nickdnj/3280-kiosk/mechanical/rev1-design-study.html

ConceptConcurrent 3280 Exhibit KioskRev 12026-08-28

# The kiosk is its own product

A self-contained enclosure — display, Pi, power, three buttons — built and bench-tested on a table, then hung on the front of the 3280's closed factory door. The machine is not opened, not drilled, not modified. The buttons are the datum: ADA reach sets their height, and the height sets where everything else goes.

Display size

22″ 24″ 27″ 32″

Button height

38″ AFF

## 01Front elevation

The kiosk on the closed factory door, drawn to scale against the 71″ cabinet with a 5′8″ figure for reference. Switch sizes above — this is the view that decides the question.

Sheet R1-01 · front elevation · cabinet 24 × 71 OEM, door 24.3 wide derived · buttons are the placement datum

The 3280 stays visually dominant. That is the whole design constraint of this view: a visitor should read a historic minicomputer with an interpretation device added to it, not a monitor wearing a cabinet.

The button line is the datum. The kiosk is placed from the bottom up: the buttons go where a hand can reach them, and the screen goes wherever that leaves it. Section 02 sets that height from the ADA reach range; the shaded band on the drawing is the legal 15″–48″ window.

Push the button slider up and the 32″ runs out of door before the others do — that constraint, not screen area, is what separates the sizes.

## 02Button height drives placement

The buttons are the datum. Where a visitor's hand goes decides where the kiosk sits, and everything above it follows. Move the slider — the elevation, the fit check and the table all follow the button line.

### The rule

ADA 2010 §308 puts operable parts between 15″ and 48″ above the finished floor. Unobstructed forward reach and unobstructed side reach give the same 48″ maximum, so the approach doesn't change the number. The 3280's face is flat and floor-standing with no knee clearance underneath, so a visitor in a wheelchair makes a parallel approach and reaches sideways — still 48″.

48″ is a ceiling, not a target

Designing at the maximum satisfies the letter of the standard and serves tall standing adults. It fails seated visitors and children, who are exactly the people the reach range exists for.

Provision | Requirement | Where it lands on this design
§308.2.1 / §308.3.1 unobstructed reach | 15″ min · 48″ max AFF | Sets the legal window for the button centreline. Binding at the top for the 32″.
§309.4 operable parts | one hand · no tight grasping, pinching or twisting · ≤ 5 lbf | A 30 mm anti-vandal momentary switch is typically well under 1 lbf. Check the actuation force on the spec sheet — some heavy industrial switches are stiff.
§305 clear floor space | 30″ × 48″ at the control | A museum floor requirement, not an enclosure one. Confirm the approach to the cabinet is kept clear when the exhibit is sited.
§307.2 protruding objects | leading edge above 27″ → 4″ max projection | Constrains the mount. See below.

### Rev 1 target — 38″ AFF

- 10″ below the ADA maximum. That margin absorbs mount tolerance, floor variation and the fact that nobody has built this yet.
- At or just above elbow height for a shorter standing adult, and a natural reach-down for a taller one.
- Comfortably inside a seated visitor's reach, and reachable by a child of about eight.

It improves the screen too

Buttons at 38″ put the 24″ screen centre at 51.5″. Adult seated eye height is roughly 47–51″, so the screen is very nearly centred on a seated visitor, while a standing adult looks down about 11° — normal reading posture. The ADA-driven placement is better for everyone than the 40″ this study first drew.

### What it costs the mount

With the buttons at 38″ the kiosk's bottom edge sits at 34.75″ AFF — above the 27″ threshold, so §307.2 caps the projection into a circulation path at 4″. With the recommended 3 mm ACM face (§06) the enclosure is 3.25″ deep, leaving 0.75″ for the mounting adapter — and a plywood face instead would cut that to 0.5″.

Worth asking, not worth assuming

§307.2 exists to stop someone with a cane walking into an object their sweep misses. The 3280 is floor-standing and cane-detectable, and a visitor is stopped by the cabinet before the kiosk is in reach — so the hazard the rule targets may not apply here. That is the museum's accessibility coordinator's call, not ours. Design the adapter to 4″ total, and ask.

### Placement math

The button centreline sits 3.25″ above the bottom of the enclosure, and the door face runs from about 3″ to 71.15″ AFF. So for a button height B and a kiosk height KH:

kiosk bottom = B − 3.25″
kiosk top = B + KH − 3.25″ ≤ 71.15″
→ B ≤ 74.40″ − KH

### The window each display size leaves you

| 22″ | 24″ | 27″ | 32″
Kiosk height | 26.69″ | 28.69″ | 31.48″ | 35.40″
Highest button the geometry allows | 47.7″ | 45.7″ | 42.9″ | 39.0″
Legal button window | 15 – 47.7″ | 15 – 45.7″ | 15 – 42.9″ | 15 – 39.0″
Of the 34–44″ comfort band | all of it | all of it | 34 – 42.9″ | 34 – 39.0″
Headroom below the door top

Correction to the earlier study

With the buttons at a properly-chosen 38″ rather than the 40″ first drawn, the 32″ fits — its top lands at 70.15″, an inch under the door. It is not a geometric failure and this study should not have called it one.

What the 32″ actually costs is freedom. It clips half the comfort band away, and the remaining inch of headroom is inside normal build tolerance. The case against it now rests on weight and proportion alone — §08.

## 03Kiosk, standalone

The enclosure by itself. Everything in this drawing is buildable and testable before the 3280 is involved at all.

Sheet R1-02 · kiosk front elevation

Sheet R1-03 · button row detail · cut into the face plate

### Why the buttons are cut straight into the face plate

An earlier version of this design put them on a separate plate behind an aperture, to insure against getting the switch cutout wrong. That was over-engineered. It bought one thing and charged three for it.

Stiffness was the real cost. Cutting both a 12.17 × 21.24 window and an 11.87 × 3.00 aperture out of one 3 mm sheet left a 1.35″ web as the only material joining the side rails below the screen. One piece leaves 2.25″ above the buttons and 2.65″ below. It also meant a second part on the invoice, six more holes, a second set of cleats, and a plate to align square in an aperture.

And the wear argument didn't hold. Anti-vandal switches are rated for millions of cycles, and when one fails you replace the switch, through the same hole. The plate only needs replacing if the hole itself is damaged, which essentially doesn't happen.

The insurance is better bought by confirming the cutout before ordering than by designing around not knowing it.

30 mm anti-vandal stainless, momentary, 30.5 mm hole. A big public target, industrial life, about $10 each, and a hole size so standard that any replacement in 2033 will fit. Labels engraved into the plate — stickers peel.

Flat, not angled. An angled lower surface adds a bevelled joint, adds depth at the bottom, and complicates the mount's load path. At 38″ AFF a flat face is comfortable for a standing adult. Revisit only if observation says otherwise.

No fasteners on the visitor-facing surface. The face plate is captured from behind — nothing on the front is a screw a bored twelve-year-old can turn.

A cleat row sits between the window and the buttons. Three fixings onto a plywood rail, so the panel takes the press load instead of flexing every time somebody pushes a button. It clears the switch bodies, which stand about an inch proud behind the plate.

## 04Side section

Depth decides how far the kiosk stands off the machine — every eighth of an inch here is visible, and ADA §307.2 caps the whole projection at 4″. Drawn with the recommended 3 mm ACM face (§06); a plywood face costs another 3/8″.

Sheet R1-04 · side section · depth to 3.5″ target · mounting interface left blank by intent

### What forces the depth

- The monitor's thickest point — 1.6″ to 2.3″. The only hard number in the stack, and the reason depth grows with screen size even though the panel doesn't.
- Cable bend at the connectors — 0.75″ to 1.75″. The one you can design away, and the difference between 3.5″ and 4.5″. Route HDMI and DC downward into the button bay with right-angle plugs.
- Face plate + rear panel. A 3 mm ACM face and a 1/2″ ply rear come to 0.62″ together. A plywood face instead makes it 1.0″ — and that 3/8″ comes straight out of the mounting adapter's budget.

### What does not

- The Raspberry Pi. 0.65″ tall, and it does not go behind the monitor. It goes in the button bay on a slide-out tray, where 4″ of depth is otherwise doing nothing. Design the enclosure around fitting a Pi behind the panel and you will build it an inch too deep.

Reversed from earlier work

The monitor stays cased. De-casing buys about 1.2″ and costs the EMI shielding, the thermal design, the power board's own enclosure, and any hope of a volunteer replacing it. Not worth it.

Depth target | Verdict
2.50″ | No. Requires a sub-1.4″ monitor, a 1/8″ face and zero service gap.
3.00″ | Achievable at 22–24″ with a slim monitor, right-angle cables and down-routing. No margin.
3.25″ | The design target, with a 3 mm ACM face. Works at 22 / 24 / 27 with 0.7″ of service air, and leaves 0.75″ for the mounting adapter under the 4″ cap.
3.50″ | What a plywood face costs you. Still fine — the mount's budget drops to 0.50″.
4.00″ | Needed for 32″, or any monitor with a rear-facing connector cluster and straight cables. Leaves nothing for the mount.

## 05Monitor comparison

Nominal sizes are marketing. These use actual diagonals — a “24-inch” panel is 23.8″. Bezel allowance +0.35″ on three sides and +0.85″ chin; face reveal 1.25″ all round; button band 6.00″ overall.

| 22″ | 24″ | 27″ | 32″
Actual diagonal | 21.5″ | 23.8″ | 27.0″ | 31.5″
Landscape active area | 18.74 × 10.54 | 20.74 × 11.67 | 23.53 × 13.24 | 27.45 × 15.44
Portrait active, W × H | 10.54 × 18.74 | 11.67 × 20.74 | 13.24 × 23.53 | 15.44 × 27.45
Portrait outline, cased | 11.74 × 19.44 | 12.87 × 21.44 | 14.44 × 24.23 | 16.64 × 28.15
Finished kiosk W × H | 14.24 × 26.69 | 15.37 × 28.69 | 16.94 × 31.48 | 19.14 × 35.40
Share of 24.3″ door width | 59% | 63% | 70% | 79%
Share of 71″ cabinet height | 38% | 40% | 44% | 50%
Kiosk top (follows the button datum)
Headroom below the 71.15″ door top
Screen centre height
Highest button the geometry allows | 47.7″ | 45.7″ | 42.9″ | 39.0″
Estimated total weight | ~20 lb | ~23 lb | ~27 lb | ~34 lb
Minimum enclosure depth | 2.4″ | 2.6″ | 2.8″ | 3.1″
Density, 1080 px across | 102 ppi | 93 ppi | 82 ppi | 70 ppi
Panel technology | IPS | IPS | IPS | often VA

### Readability governs, resolution doesn't

The real constraint is cap height. Comfortable reading at 6 ft wants roughly 0.35″ of cap height — about a half-inch em. On the 24″, 20.74″ tall across 1920 px, that is a 46 px body size, giving about 47 characters per line. A good measure for the 3–5 bullets per screen the content bar allows.

The 22″ lands at ~42 characters. Workable, but it starts to constrain the writing. All four are legible at 3–6 ft; a 1080p 24″ at 93 ppi is crisp at arm's length and dead sharp at exhibit distance. Don't pay for 1440p unless the salvage pile hands it to you.

## 06What it's made of, and where to buy it

Three ways to build the box. What separates them isn't strength and it isn't cost — it's whether the finished thing looks bought or looks homemade.

### First: what these materials actually are

#### ACM

aluminium composite · “Dibond”

Two thin sheets of aluminium glued either side of a plastic core — a metal sandwich about 1/8″ thick. Stiff, dead flat, and the colour is baked onto the aluminium at the factory. Nothing to sand, nothing to paint. Almost every storefront sign and road sign you've ever looked at is this stuff.

#### HPL

high-pressure laminate · “Formica”

The material on a kitchen counter. Here's the catch: it is not a board. It's a 1/32″ skin with no stiffness of its own, so it has to be glued down onto plywood or MDF first. That gluing step is the word “bonded” doing a lot of quiet work.

#### Compact laminate

solid phenolic · Trespa, Fundermax

The same material as Formica, but pressed thick enough to stand on its own — 1/4″ to 1/2″. Restroom partitions and school lab benches. Beautiful and effectively permanent, but heavy and mostly sold in architectural quantities.

#### Baltic birch

void-free plywood

Very good plywood — many thin layers, no hidden gaps inside. Strong, and it machines beautifully. But it is wood: to look finished it wants sanding, sealing and spraying, and that is where volunteer builds usually come unstuck.

### The three routes

#### A · Plywood, cut and sprayed

the traditional way

What you do

CNC-cut 1/2″ Baltic birch, rabbet the corners, spray satin graphite.

The hard part

The finish. Ply edges telegraph through paint and a brushed coat reads homemade from ten feet away.

Needs

CNC access and somewhere to spray.

Material

~$80–140

Weight

~13 lb enclosure

- Where to buy the plywood
- MakerStock — 1/2″ Baltic birch, custom cuts (https://makerstock.com/collections/baltic-birch-plywood) up to 24 × 48
- Cherokee Wood Products — cut to size (https://www.cherokeewood.com/store/1-2-baltic-birch-plywood-cut-to-size/)
- Woodworkers Source — pre-cut packs (https://www.woodworkerssource.com/plywood/12-baltic-birch-plywood-pack-choose-your-size.html)
- Jeff Mack Supply — pick a size (https://jeffmacksupply.com/en-us/products/1-2-thick-baltic-birch-select-a-size)

#### B · Plywood box, ACM front

recommended

What you do

The same plywood box — but the visible front is 3 mm black ACM, cut to shape and screwed to cleats inside.

Why it wins

The face arrives already finished. No spray booth, no grain to fill, no sanding, nothing to get wrong on the one surface everybody looks at.

Needs

Ordinary woodworking. The front gets cut by someone else — see below.

Material

~$120–200

Weight

~12 lb — about a pound lighter than A, since ACM replaces the plywood front

- Where to buy the ACM
- SendCutSend — cut to our shape (https://sendcutsend.com/materials/acm/) best option, see below
- Curbell Plastics — Dibond sheet (https://www.curbellplastics.com/product-category/material/aluminum-composite-material-acm/dibond-panels/)
- OnlineMetals — 3 mm black ACM (https://www.onlinemetals.com/en/buy/3mm-aluminum-composite-panel-black/pid/mp-00040256)
- Midwest Airbrush — small black pieces (https://www.midwestairbrush.com/collections/acm-aluminum-panels-black)
- If you'd rather use Formica
- Wilsonart vertical grade, black matte (https://www.amazon.com/Wilsonart-Sheet-Laminate-Vertical-Grade/dp/B01FV20Z6A)
- Ledgeband — Formica / Wilsonart, no minimum (https://ledgeband.com/collections/laminate-sheets)

#### C · Modify a bought enclosure

doesn't fit

What you do

Buy a digital-signage or instrument housing and cut it for the panel.

Why it fails

Nothing off the shelf is 15″ × 29″ × 3-1/4″ portrait. Everything close is a landscape signage box or a deep electrical enclosure.

Worth

Ten minutes of searching. Not worth designing around.

Material

$150–400

Weight

30 lb+ in steel

- If you want to look anyway
- Fundermax — compact phenolic panels (https://fundermax.us/product/interior-thin-laminate-panels/)
- Wilsonart Compact laminate (https://www.wilsonart.com/laminate/specialty-laminate/compact)

The move that actually makes this easy

Don't buy a sheet. Send the file.

SendCutSend (https://sendcutsend.com/materials/acm/) will CNC-route the face plate out of 3 mm matte black ACM and mail it to you. You upload a drawing file, they cut it to ±0.005″, and it ships in 2–4 days.

Their maximum part is 30″ × 44″. Our face plate is 15.4 × 28.7 — well inside it.

This takes the hardest job away from the volunteer crew entirely: no CNC access needed at CDL, no 4 × 8 sheet to buy and mostly throw away, no jig for the big screen window, and the three button holes arrive already cut to size. What's left is building a plywood box — which is the part any woodworker gets right the first time.

### One small thing that decides the material

Panel-mount buttons have a maximum panel thickness — how thick a face they can clamp through. It's model-specific, commonly somewhere between 6 and 11 mm.

3 mm ACM clears every one of them. A 1/2″ plywood-and-Formica face is 12.7 mm — at or over the limit for most switches, which means counterboring the back of all three holes by hand. Small detail, real annoyance, and it points the same way as everything else. It matters more now that the buttons are cut straight into the face plate (§03) — there is no thin sub-plate to fall back on.

Two limits on ACM worth knowing

It can't be tapped or bent. Fastening goes through clearance holes into threaded inserts in the plywood cleats — which was already the plan.

Cut edges show the black plastic core. On a black panel that's invisible. On white it's a visible dark line — one more reason to order it black on both sides.

### Shopping list

Part | What to order | Where | Rough cost
Face plate | 3 mm ACM, matte black both sides. File ready: P1-face-plate.dxf — buttons cut in, one piece | SendCutSend (https://sendcutsend.com/materials/acm/) | quote on upload qty 1
Box — sides, top, bottom, rear panel | 1/2″ Baltic birch, about 8 sq ft | MakerStock (https://makerstock.com/collections/baltic-birch-plywood) · Cherokee (https://www.cherokeewood.com/store/1-2-baltic-birch-plywood-cut-to-size/) | $40–90
Buttons × 3 | 30 mm anti-vandal, momentary, stainless. Check two things on the datasheet: panel range includes 3 mm, and actuation force ≤ 5 lbf (§309.4) | APEM AV series (https://www.apem.com/panel-switches/pushbutton-switches/av-anti-vandal-pushbutton-switches) · RJS (https://www.rjselectronics.com/category/panel-mount/pushbutton-metal-switches/metal-pushbutton-switches-anti-vandal/) · Adafruit (https://www.adafruit.com/category/235) (arcade alt) | $25–40
Threaded inserts | #8 for plywood, ×15 — never screw into a plywood edge | McMaster-Carr, or any hardware store | ~$12
Rear-panel fasteners | Quarter-turn fasteners or captive thumbscrews, ×6. Captive so nothing drops inside a museum artifact | McMaster-Carr | $20–30

Costs are estimates — confirm at the link before you budget. Every link here was checked; Curbell and OnlineMetals block automated requests, so they load in a browser but not from a script.

The cut files exist — you can order today

mechanical/fab-rev1/P1-face-plate.dxf — one part, generated from the geometry on this page and self-checked for closed contours, holes clear of the window, feature spacing and minimum hole size against 3 mm material, and that the button datum still lands at 25.440″.

15.37 × 28.69″ · screen window 12.17 × 21.24 · three ⌀30.5 mm at 3.50″ centres · fifteen ⌀0.1875 mounting holes around the perimeter and on a cleat row above the buttons.

Upload it, choose ACM → 0.118″ (3 mm) → matte black, quantity 1. No secondary services — ACM can't be bent, tapped or countersunk, and none of it is needed.

⚠ Confirm one number before you press order. ⌀30.5 mm is the cutout for a “30 mm” anti-vandal switch, and most want 30.2–30.5 mm. Cutting the larger size is the safe direction — the nut and washer cover slack — but this is a one-piece part, so a wrong cutout means recutting the whole face. Check it against the datasheet of the switch you actually buy, along with panel range including 3 mm and actuation force ≤ 5 lbf.

Why the face plate is safe to cut before the monitor arrives

The screen window is 0.25″ oversize per side, on purpose. “24 inch” covers 23.6″–24.0″ diagonals and this window clears every one of them without cropping a pixel — and the margin falls on the monitor's own black bezel, so behind a black face plate nothing shows.

The monitor is aligned to the window, not the other way round: it hangs on a VESA plate on an internal frame, so whatever offset a particular model has between its panel and its VESA pattern gets taken up there.

### Labels

There's no text in the cut files. BACK / HOME / NEXT is a separate step, and the native answer for ACM is cut vinyl from a sign shop — this is sign material, and it's how every road sign in the country is lettered. Durable, cheap, replaceable. Ask SendCutSend whether they'll engrave ACM first; if they will, that's better still.

### Serviceability

The rule: nothing that fails routinely should require touching the face plate or the mount. The kiosk should never have to come off the 3280 for service.

Part | How it comes out
Rear panel | Captive thumbscrews or quarter-turn fasteners into threaded inserts. No loose hardware to drop inside a museum artifact.
Monitor | On a VESA 100 plate bolted to the internal frame. Rear panel off, four bolts, monitor out backwards. The face plate never comes off.
Raspberry Pi | Slide-out tray in the button bay. Unplug two, slide out.
Buttons | Plate captured from behind. Rear panel off, plate drops in. Standard 30.5 mm hole.
Power | One appliance inlet at the bottom rear. One cord leaves the kiosk.

## 07Attachment interface

Deliberately not designed. The enclosure's job here is to have a flat back and a known weight — that is enough for an adapter to be designed against later, and designing it now would be guessing.

Sheet R1-05 · rear · mounting interface zone, design TBD

### Constraints recorded now, so the enclosure doesn't foreclose them

- Reversible, non-destructive, removable, visually discreet. No holes, no cuts, no permanent modification to the door or the cabinet. This is a hard requirement, not a preference — the 3280 is a museum artifact.
- Must carry the kiosk in shear plus the moment from a centre-of-mass roughly 1.6″ off the door, with a safety factor for someone leaning on it.
- Total projection from the door face should stay at or under 4″ (§307.2 — the kiosk's leading edge is at 34.75″ AFF, above the 27″ threshold). The enclosure is 3.25″, so the adapter's budget is 0.75″.
- Candidates, unevaluated: edge brackets hooking the door's return flange; compression straps around the cabinet; a full-door backing plate captured top and bottom; clamps on existing door hardware.
- Anything that loads the original hinges has to be checked against them.

This is why weight matters

The mount is undesigned and unconstrained. 23 lb of strap-and-bracket load on a hollow sheet-metal door is a solvable problem. 34 lb is where you start having to transfer load to the cabinet frame — and the mount stops being simple. That, more than proportion, is the argument against the 32″.

## 08Recommendation

Rev 1

24″-class display, 23.8″ actual. Finished kiosk 15-3/8″ W × 28-11/16″ H × 3-1/4″ D, about 23 lb.

Buttons 38″ AFF · kiosk bottom 34.75″ · kiosk top 63.44″ · screen centre 51.5″ · 7.71″ headroom · 3 mm ACM face on a Baltic birch box

Proportion is the deciding argument. At 15.4″ wide the kiosk is 63% of the door — clearly an added object, clearly not trying to be the machine. At 70% and 79% the 27″ and 32″ start to read as a monitor wearing a cabinet, which is precisely the impression a museum exhibit should not give.

Weight is the second argument, and it may be the more important one — see section 06. The mount has to carry this off a hollow door without a single fastener into the artifact.

Availability closes it. 24″ 1080p IPS is the highest-volume monitor ever made. It is the most likely thing in the warehouse, the cheapest thing to buy, and the easiest thing for a docent to replace in 2033 without calling anyone.

### If a 27″ falls out of the salvage pile

Take it. It isn't a bad answer — it's a slightly worse answer, and the enclosure is parametric enough that switching costs one face plate. Budget the extra 4 lb into the mount. 22″ is the fallback if the mount turns out harder than expected; 20 lb is genuinely easy to hang. 32″ is out — but not for the reason this study first gave. With the buttons properly placed at 38″ it fits the door with an inch to spare (§02). It goes because of the weight, the proportion, and the VA-panel risk: visitors approach an exhibit from the side, and a VA panel at 45° looks bad in exactly that situation. It also leaves an inch of headroom against build tolerance and clips half the comfortable button band away.

Two go/no-go criteria on any candidate monitor

1 · It must power itself back on after a mains cut. The exhibit runs on an AC timer. Many monitors return to standby and need a button press — that's a black screen every morning until a docent notices. Test before committing: switched strip, kill power, restore, confirm it comes back with no input.

2 · Matte only. Overhead lights and daylight. Glossy panels mirror them.

### Sequence

1. Choose the monitor. Buy or salvage; run the power-cut test. Gate — everything downstream is dimensioned off this.
2. Build the enclosure. Bench, no 3280 involved.
3. Install monitor, Pi, buttons, wiring, software.
4. Bench-test as a complete kiosk. Run it for a week on a table.
5. Then design and build the reversible mounting adapter.
6. Rev 2, if desired, revisits the replacement-door concept.

Steps 1–4 have no dependency on the 3280 at all. C1 — the closing clearance that gated the entire previous design — no longer gates anything, and neither does the door height, the aperture, or the inner perforated panel.

Superseded for Rev 1, kept for provenance and live for Rev 2: the 27″ call in monitor-selection.md, the hinged-carrier route in display-approach-options.md, the de-cased-panel route in door-construction.md and fab/, and drawings 01–06 in drawings/.

Cabinet 71 × 24 × 34 from Concurrent 50-045R00 · box height 67-7/8″ measured ME-1 · door 24.3″ from Perkin-Elmer 47-004 R21 · factory paint P.E. #464 textured. Monitor outlines, weights and thicknesses are estimates from typical current product, not measured units.

3280-kiosk · mechanical/rev1-design-study.html · concept, not a shipped product
