nickdnj/3280-kiosk/mechanical/dwg/index.html

# Concurrent 3280 Exhibit Kiosk — Rev 1

Manufacturing drawing package · 12 sheets · B size (17 × 11) · third angle · concept, not released for production

To print: ⌘P — the print stylesheet puts one sheet per page, Letter landscape. Choose Fit to page; these are reference drawings, not cut at scale. “Save as PDF” in the same dialog gives you the whole package as one file.

## 000COVER · DRAWING INDEX · GENERAL NOTES

Sheet 000

## 100ASSEMBLY · GENERAL ARRANGEMENT · INSTALLED CONTEXT

Sheet 100

## 101ASSEMBLY · EXPLODED · BILL OF MATERIALS

Sheet 101

## 102ASSEMBLY · SECTION A-A · DEPTH CHAIN

Sheet 102

## 200P1 FACE PLATE · ACM · CUT DRAWING

Sheet 200

## 300P2 SIDE PANEL · P3 TOP AND BOTTOM PANEL

Sheet 300

## 301P4 REAR PANEL · P9 VESA RAIL · P10 PI TRAY

Sheet 301

## 302P5 TO P8 CLEATS AND BUTTON RAIL

Sheet 302

## 400HOLE AND FASTENER SCHEDULE

Sheet 400

## 500ELECTRICAL SCHEMATIC AND WIRING

Sheet 500

## 600ASSEMBLY SEQUENCE

Sheet 600

## 700INSPECTION DIMENSIONS AND SIGN-OFF

Sheet 700
