nickdnj/3280-kiosk/mechanical/dwg/3280-kiosk-rev1-drawing-package.pdf

# CONCURRENT 3280 EXHIBIT KIOSK

## REV 1 · STANDALONE ENCLOSURE · MANUFACTURING PACKAGE

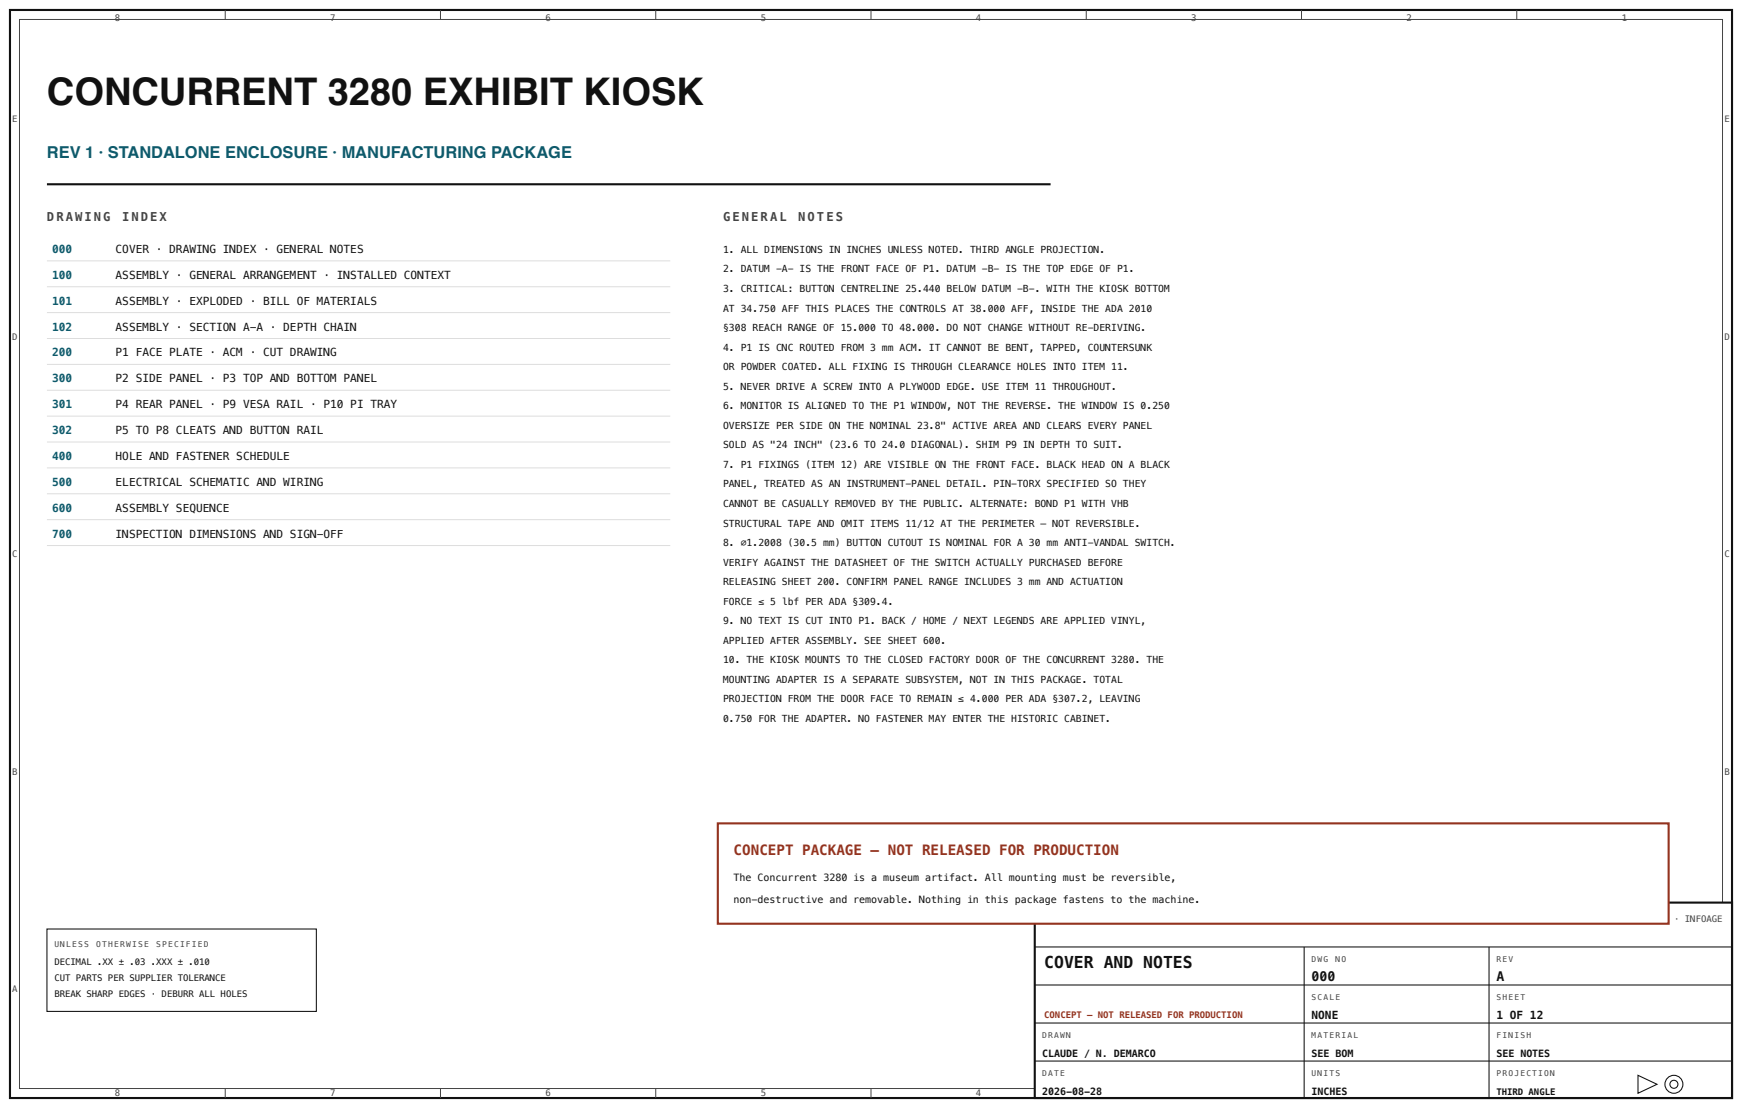
[picture p3: page 1]

000 COVER · DRAWING INDEX · GENERAL NOTES

1. ALL DIMENSIONS IN INCHES UNLESS NOTED. THIRD ANGLE PROJECTION.
2. DATUM -A- IS THE FRONT FACE OF P1. DATUM -B- IS THE TOP EDGE OF P1.
3. CRITICAL: BUTTON CENTRELINE 25.440 BELOW DATUM -B-. WITH THE KIOSK BOTTOM
AT 34.750 AFF THIS PLACES THE CONTROLS AT 38.000 AFF, INSIDE THE ADA 2010
§308 REACH RANGE OF 15.000 TO 48.000. DO NOT CHANGE WITHOUT RE-DERIVING.
4. P1 IS CNC ROUTED FROM 3 mm ACM. IT CANNOT BE BENT, TAPPED, COUNTERSUNK
OR POWDER COATED. ALL FIXING IS THROUGH CLEARANCE HOLES INTO ITEM 11.
5. NEVER DRIVE A SCREW INTO A PLYWOOD EDGE. USE ITEM 11 THROUGHOUT.
6. MONITOR IS ALIGNED TO THE P1 WINDOW, NOT THE REVERSE. THE WINDOW IS 0.250
OVERSIZE PER SIDE ON THE NOMINAL 23.8" ACTIVE AREA AND CLEARS EVERY PANEL
SOLD AS "24 INCH" (23.6 TO 24.0 DIAGONAL). SHIM P9 IN DEPTH TO SUIT.
7. P1 FIXINGS (ITEM 12) ARE VISIBLE ON THE FRONT FACE. BLACK HEAD ON A BLACK
PANEL, TREATED AS AN INSTRUMENT-PANEL DETAIL. PIN-TORX SPECIFIED SO THEY
CANNOT BE CASUALLY REMOVED BY THE PUBLIC. ALTERNATE: BOND P1 WITH VHB
STRUCTURAL TAPE AND OMIT ITEMS 11/12 AT THE PERIMETER — NOT REVERSIBLE.
8. ⌀1.2008 (30.5 mm) BUTTON CUTOUT IS NOMINAL FOR A 30 mm ANTI-VANDAL SWITCH.
VERIFY AGAINST THE DATASHEET OF THE SWITCH ACTUALLY PURCHASED BEFORE
RELEASING SHEET 200. CONFIRM PANEL RANGE INCLUDES 3 mm AND ACTUATION
FORCE ≤ 5 lbf PER ADA §309.4.
9. NO TEXT IS CUT INTO P1. BACK / HOME / NEXT LEGENDS ARE APPLIED VINYL,
APPLIED AFTER ASSEMBLY. SEE SHEET 600.
10. THE KIOSK MOUNTS TO THE CLOSED FACTORY DOOR OF THE CONCURRENT 3280. THE
MOUNTING ADAPTER IS A SEPARATE SUBSYSTEM, NOT IN THIS PACKAGE. TOTAL
PROJECTION FROM THE DOOR FACE TO REMAIN ≤ 4.000 PER ADA §307.2, LEAVING
0.750 FOR THE ADAPTER. NO FASTENER MAY ENTER THE HISTORIC CABINET.

100 ASSEMBLY · GENERAL ARRANGEMENT · INSTALLED CONTEXT

101 ASSEMBLY · EXPLODED · BILL OF MATERIALS

102 ASSEMBLY · SECTION A-A · DEPTH CHAIN

200 P1 FACE PLATE · ACM · CUT DRAWING

300 P2 SIDE PANEL · P3 TOP AND BOTTOM PANEL

301 P4 REAR PANEL · P9 VESA RAIL · P10 PI TRAY

302 P5 TO P8 CLEATS AND BUTTON RAIL

400 HOLE AND FASTENER SCHEDULE

500 ELECTRICAL SCHEMATIC AND WIRING

700 INSPECTION DIMENSIONS AND SIGN-OFF

CONCEPT PACKAGE — NOT RELEASED FOR PRODUCTION

The Concurrent 3280 is a museum artifact. All mounting must be reversible,
non-destructive and removable. Nothing in this package fastens to the machine.

DECIMAL .XX ± .03 .XXX ± .010
CUT PARTS PER SUPPLIER TOLERANCE
BREAK SHARP EDGES · DEBURR ALL HOLES

CONCEPT — NOT RELEASED FOR PRODUCTION

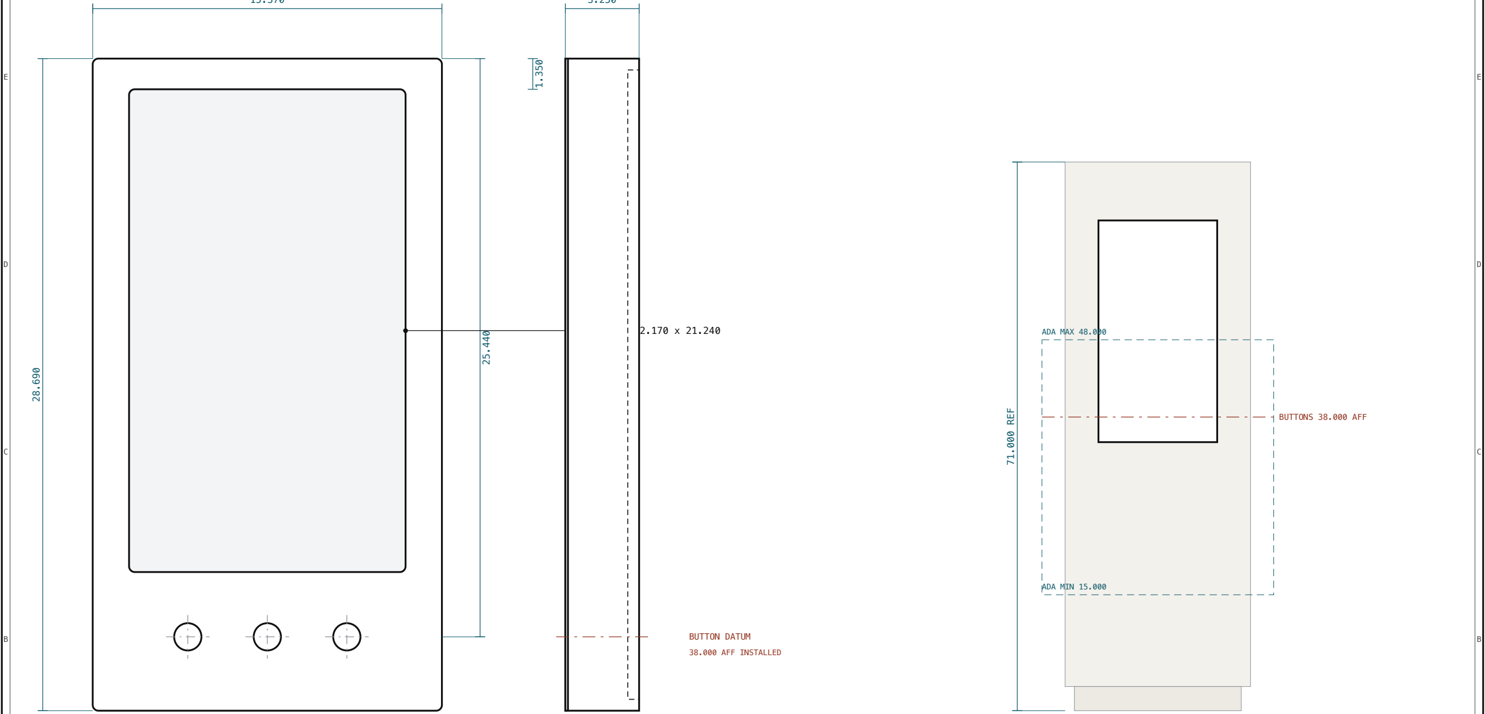
[picture p4: figure]
WINDOW 12.170 x 21.240; BUTTON DATUM; 38.000 AFF INSTALLED; ADA MAX 48.000; ADA MIN 15.000; BUTTONS 38.000 AFF; 71.000 REF

A | A
3 2 8 0 K I O S K · R E V 1 S T A N D A L O N E | VINTAGE COMPUTER FEDERATION · INFOAGE

# GENERAL ARRANGEMENT

CONCEPT — NOT RELEASED FOR PRODUCTION

D W G N O
100

R E V
A

S C A L E
1:4

S H E E T

### 2 OF 12

ASSEMBLY

—

## FRONT

15.370

3.500

## RIGHT SIDE

3.250

## TOP

INSTALLED CONTEXT — REFERENCE ONLY

CONCURRENT 3280, DOOR CLOSED

U N L E S S O T H E R W I S E S P E C I F I E D
DECIMAL .XX ± | .03 .XXX ± .010
CUT PARTS PER | SUPPLIER TOLERANCE
BREAK SHARP EDGES · DEBURR ALL HOLES

1

5

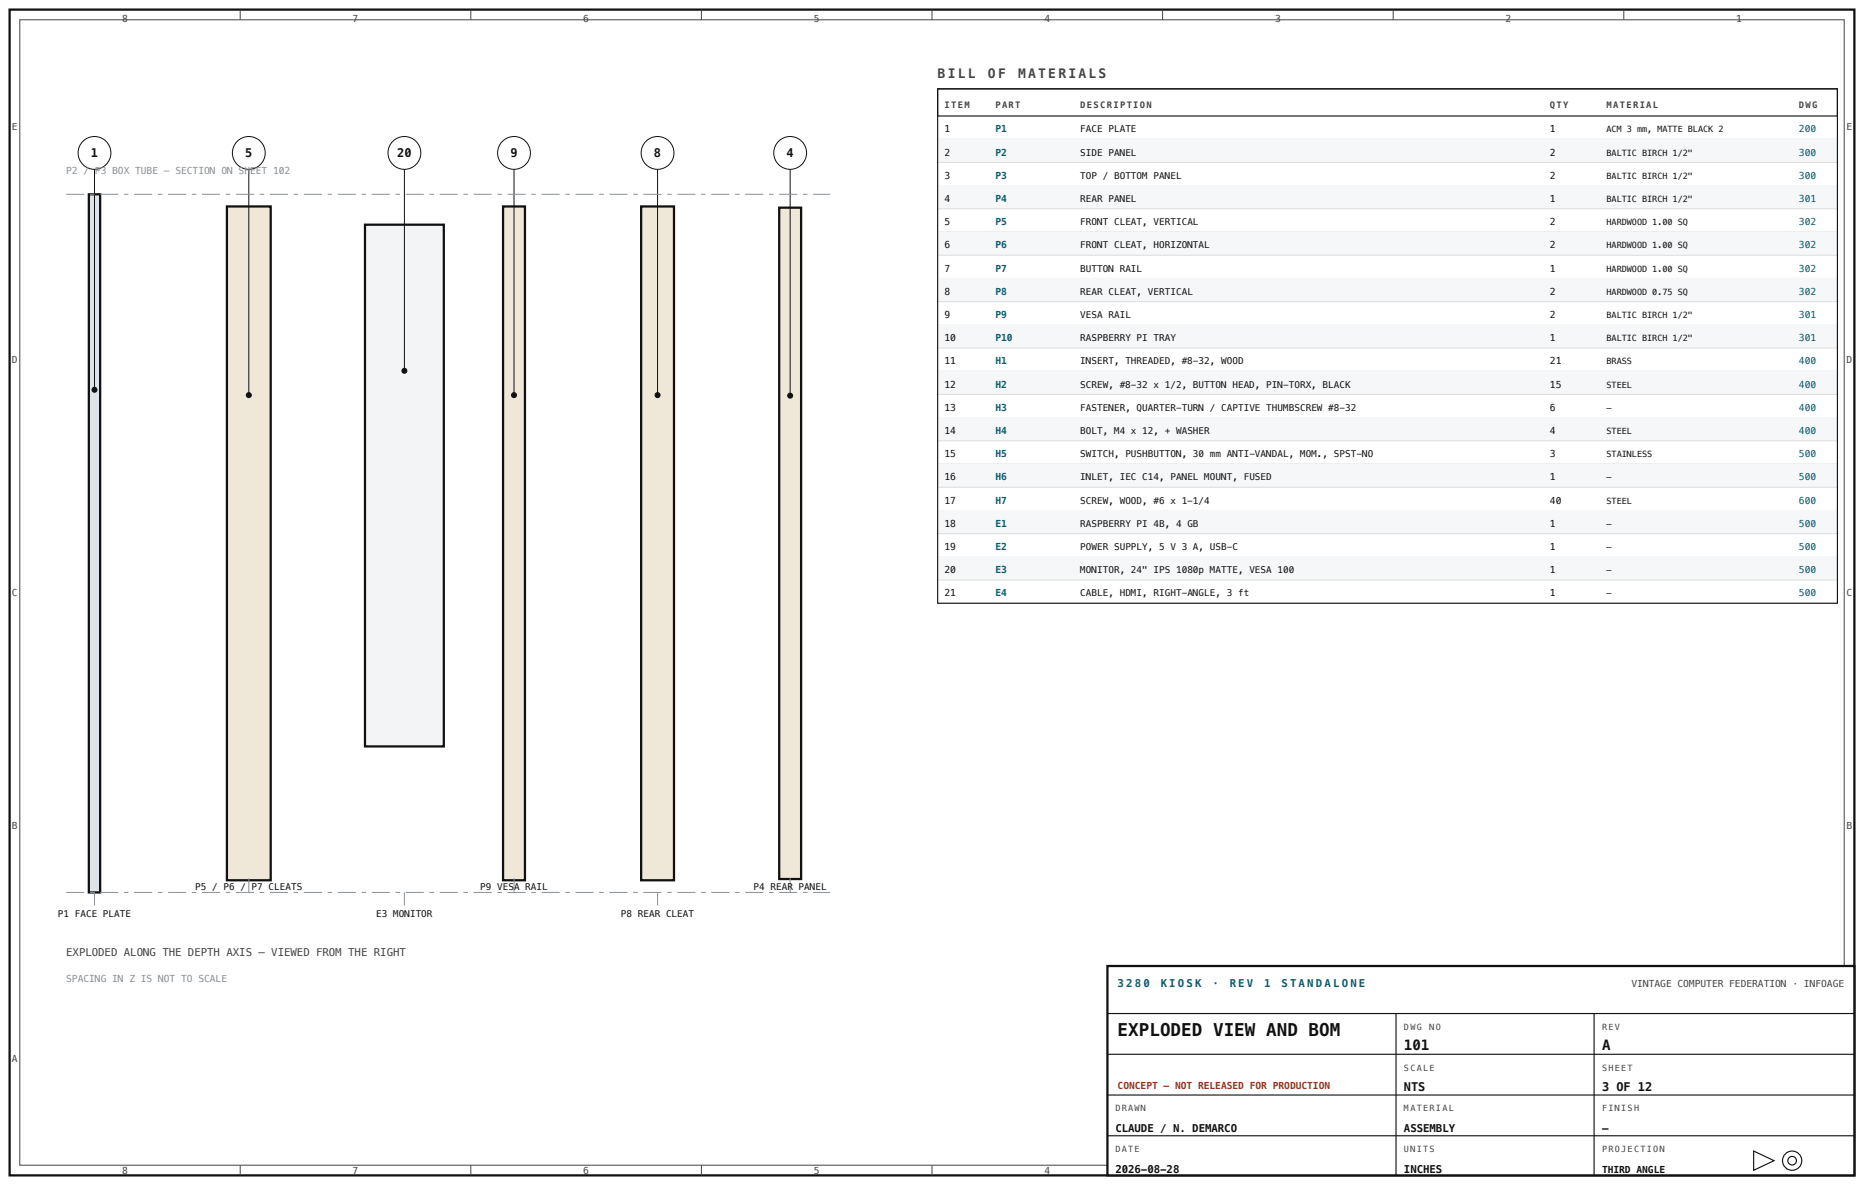
[picture p5: page 3]

EXPLODED ALONG THE DEPTH AXIS — VIEWED FROM THE RIGHT

SPACING IN Z IS NOT TO SCALE

EXPLODED VIEW AND BOM

CONCEPT — NOT RELEASED FOR PRODUCTION

28.690

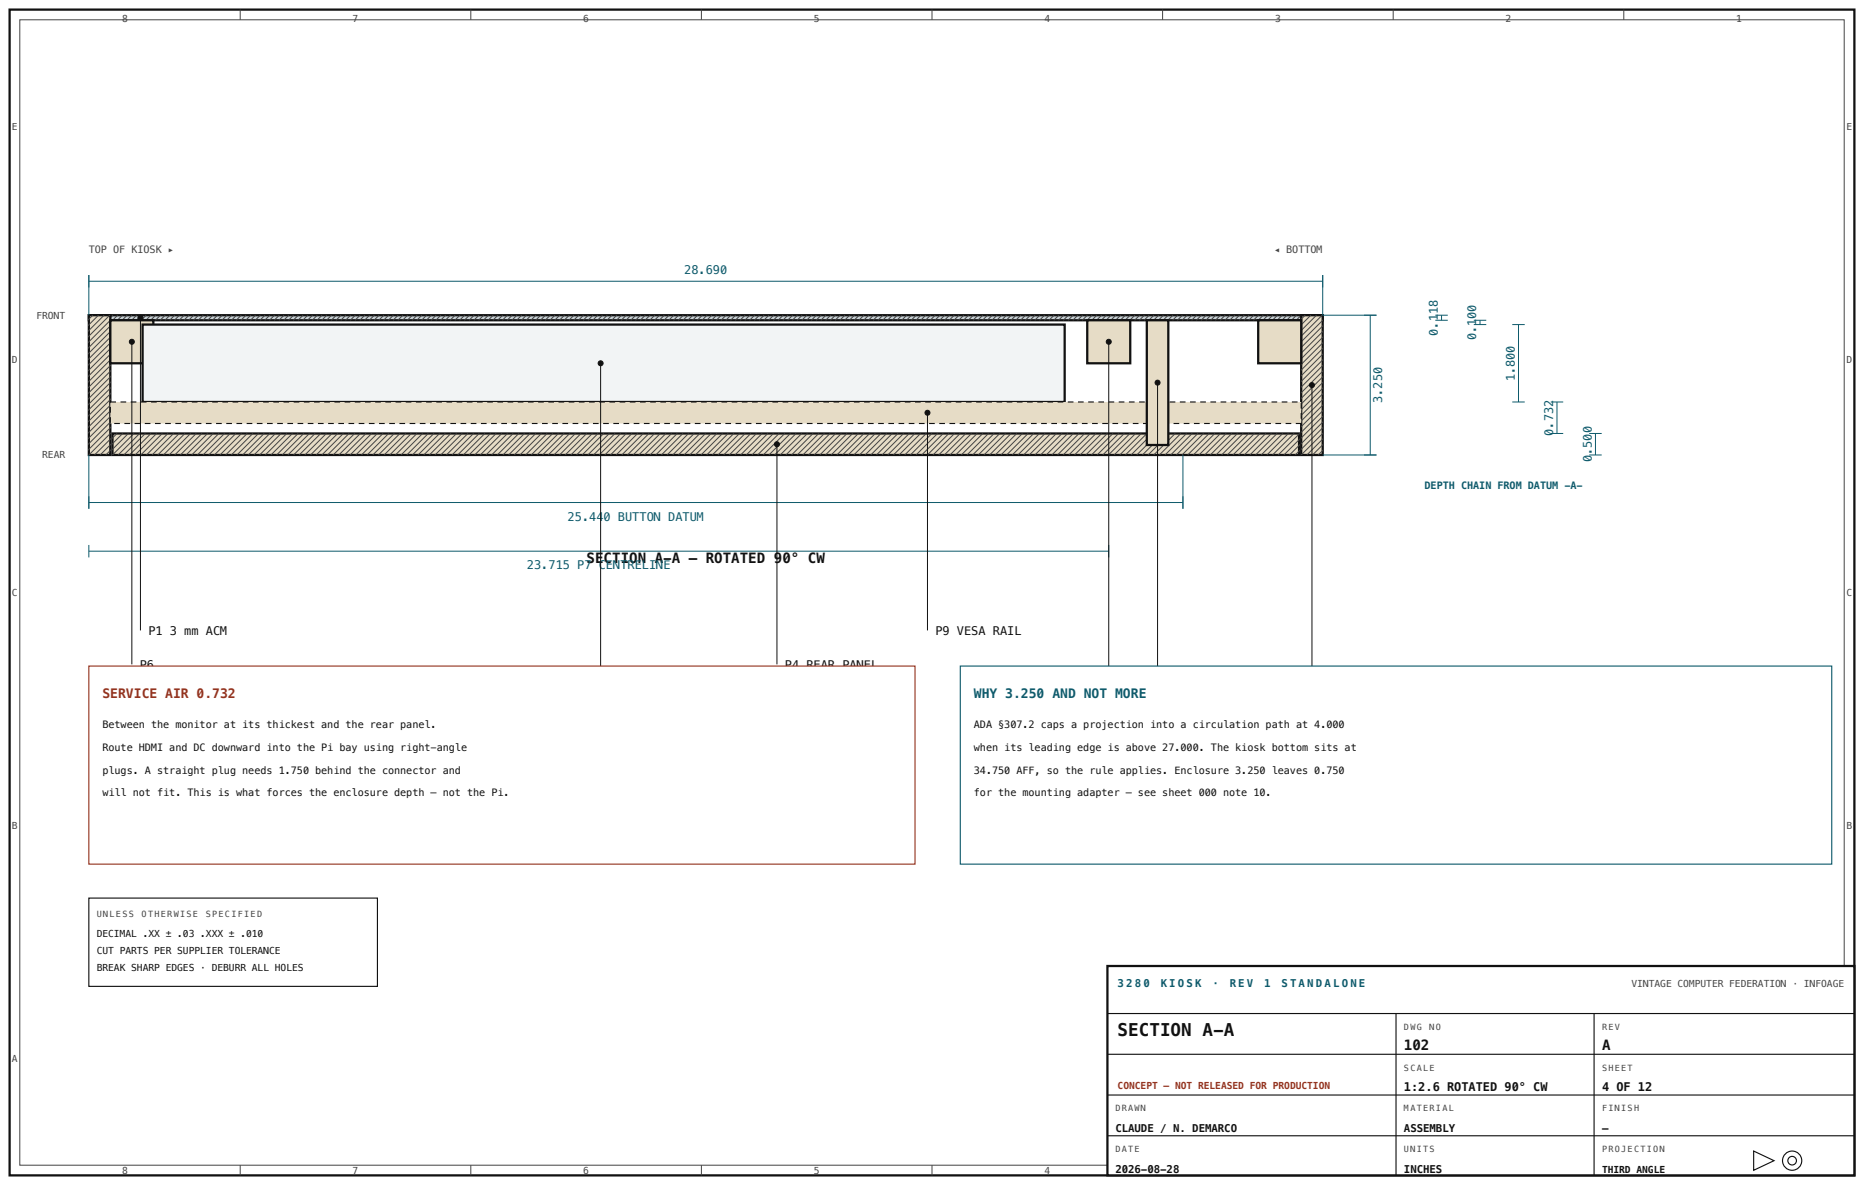
[picture p6: page 4]
VINTAGE COMPUTER FEDERATION · INFOAGE; SECTION A-A; S C A L E 1:2.6 ROTATED 90° CW; ASSEMBLY; TOP OF KIOSK ▸; ◂ BOTTOM; FRONT; REAR; 25.440 BUTTON DATUM; CENTRELINE; P1 3 mm ACM; P7 BUTTON RAIL; P9 VESA RAIL; P4 REAR PANEL; P10 PI TRAY; SERVICE AIR 0.732; WHY 3.250 AND NOT; MORE; ADA §307.2 caps a projection into a circulation path at

DEPTH CHAIN FROM DATUM -A-

SECTION A-A — ROTATED 90° CW

Between the monitor at its thickest and the rear panel.

E3 MONITOR — 1.800 AT THICKEST

Route HDMI and DC downward into the Pi bay using right-angle

when its leading edge is above 27.000. The kiosk bottom sits at

plugs. A straight plug needs 1.750 behind the connector and

34.750 AFF, so the rule applies. Enclosure 3.250 leaves 0.750

will not fit. This is what forces the enclosure depth — not the Pi.

for the mounting adapter — see sheet 000 note 10.

DECIMAL .XX ± .03 .XXX ± .010
CUT PARTS PER SUPPLIER TOLERANCE
BREAK SHARP EDGES · DEBURR ALL HOLES

CONCEPT — NOT RELEASED FOR PRODUCTION

15.370

12.170

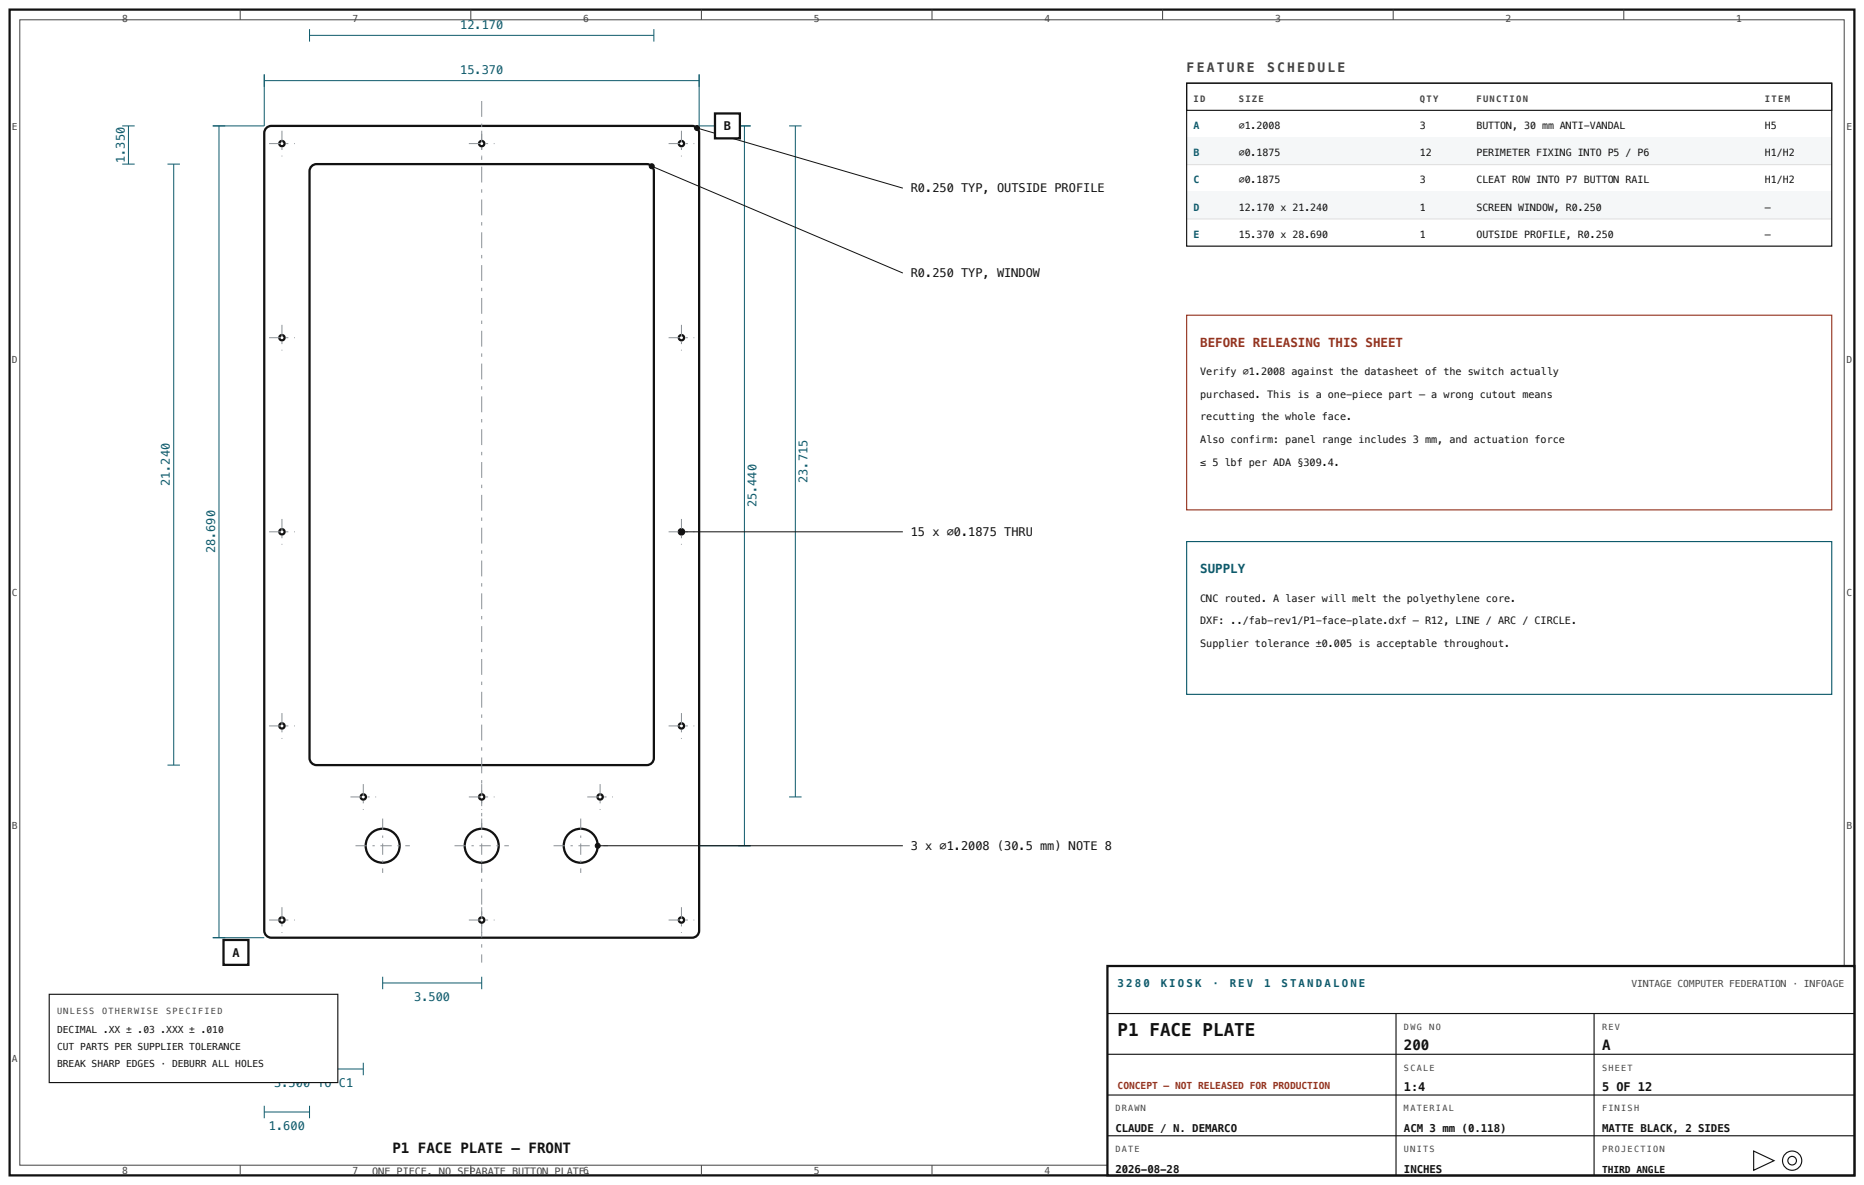
[picture p7: page 5]
VINTAGE COMPUTER FEDERATION · INFOAGE; P1 FACE PLATE; ACM 3 mm (0.118); 3 x ⌀1.2008 (30.5 mm) NOTE 8; 15 x ⌀0.1875 THRU; R0.250 TYP, WINDOW; BUTTON, 30 mm ANTI-VANDAL; PERIMETER FIXING INTO P5 / P6; CLEAT ROW INTO P7 BUTTON RAIL; SCREEN WINDOW, R0.250; OUTSIDE PROFILE, R0.250; SUPPLY

R0.250 TYP, OUTSIDE PROFILE

BEFORE RELEASING THIS SHEET

Verify ⌀1.2008 against the datasheet of the switch actually

purchased. This is a one-piece part — a wrong cutout means

recutting the whole face.

Also confirm: panel range includes 3 mm, and actuation force

≤ 5 lbf per ADA §309.4.

CNC routed. A laser will melt the polyethylene core.

DXF: ../fab-rev1/P1-face-plate.dxf — R12, LINE / ARC / CIRCLE.

Supplier tolerance ±0.005 is acceptable throughout.

DECIMAL .XX ± .03 .XXX ± .010
CUT PARTS PER SUPPLIER TOLERANCE
BREAK SHARP EDGES · DEBURR ALL HOLES

CONCEPT — NOT RELEASED FOR PRODUCTION

MATTE BLACK, 2 SIDES

P1 FACE PLATE — FRONT

ONE PIECE. NO SEPARATE BUTTON PLATE.

E | E
D | D
C | C
B | B
A | A
3 2 8 0 K I O S K · R E V 1 S T A N D A L O N E | VINTAGE COMPUTER FEDERATION · INFOAGE

# P2 / P3 BOX PANELS

CONCEPT — NOT RELEASED FOR PRODUCTION

D W G N O
300

R E V
A

S C A L E
1:4

S H E E T

### 6 OF 12

BALTIC BIRCH 1/2 (0.500)

SEALED, SATIN BLACK INSIDE

3.132

28.690

### P2 SIDE PANEL QTY 2

BALTIC BIRCH 1/2"

3.132

14.370

### P3 TOP / BOTTOM QTY 2

BALTIC BIRCH 1/2"

## B O X A S S E M B L Y — P L A N

### 15.370 OVERALL

### 14.370 CAVITY

3.250

P1

P2

P5

P8

P9

P4

HORIZONTAL SECTION THROUGH THE MONITOR ZONE — SCALE 1:2.6

### BOX CONSTRUCTION

P2 SIDES RUN FULL HEIGHT 28.690 AND CAPTURE P3.

P3 TOP AND BOTTOM ARE 14.370 BETWEEN THE SIDES.

GLUE AND SCREW WITH ITEM 17, #6 x 1-1/4, 4 PER JOINT,

PILOT DRILLED. CLAMP SQUARE — DIAGONALS WITHIN 0.06.

CLEATS P5/P6 GLUE FLUSH WITH THE FRONT EDGE.

REAR CLEATS P8 SET BACK 0.750 FROM THE REAR EDGE SO

P4 FINISHES FLUSH.

SEAL AND PAINT ALL INTERNAL SURFACES SATIN BLACK

BEFORE ASSEMBLY — REFLECTIONS SHOW THROUGH THE WINDOW.

GRAIN DIRECTION: LONG AXIS OF EACH PART.

U N L E S S O T H E R W I S E S P E C I F I E D DECIMAL .XX ± .03 .XXX ± .010
CUT PARTS PER SUPPLIER TOLERANCE BREAK SHARP EDGES · DEBURR ALL HOLES

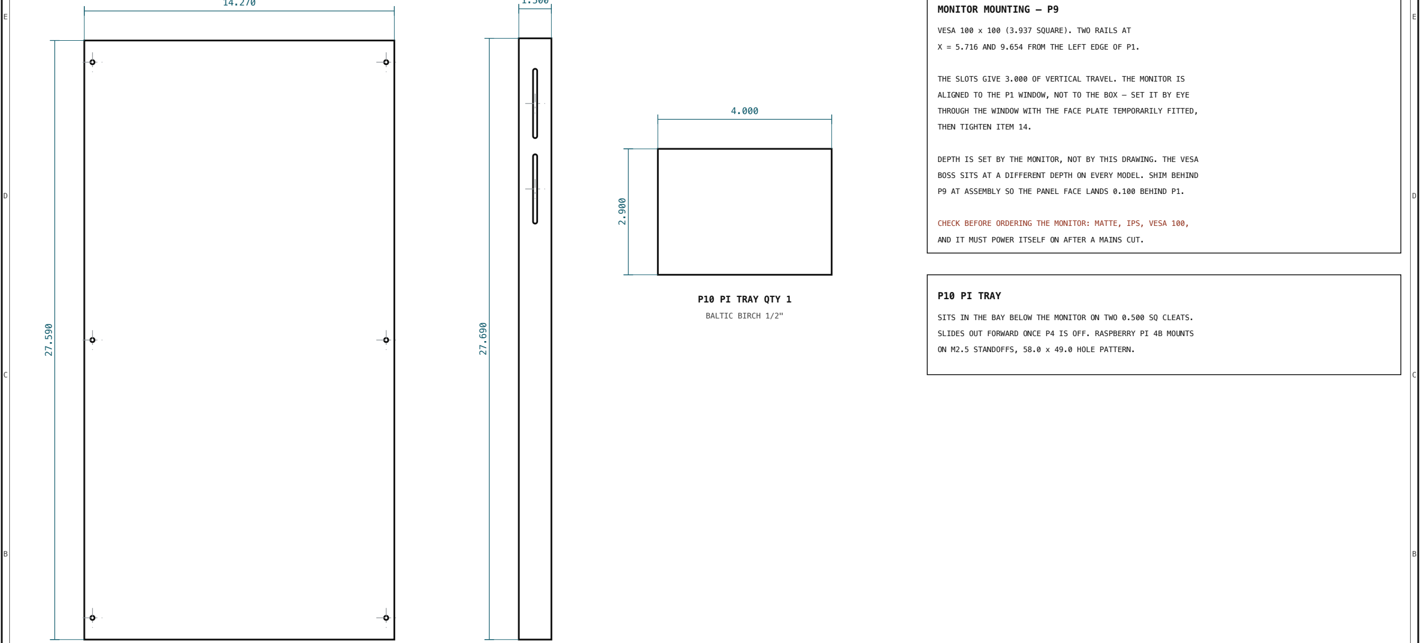
[picture p8: figure]
P10 PI TRAY QTY 1; BALTIC BIRCH 1/2"; MONITOR MOUNTING — P9; THEN TIGHTEN ITEM 14.; P10 PI TRAY

A | A
3 2 8 0 K I O S K · R E V 1 S T A N D A L O N E | VINTAGE COMPUTER FEDERATION · INFOAGE

# P4 / P9 / P10

CONCEPT — NOT RELEASED FOR PRODUCTION

D W G N O
301

R E V
A

S C A L E
1:4

S H E E T

### 7 OF 12

BALTIC BIRCH 1/2 (0.500)

SEALED, SATIN BLACK

14.270

### P4 REAR PANEL QTY 1

BALTIC BIRCH 1/2"

6 x ⌀0.190 FOR ITEM 13

1.500

### P9 VESA RAIL QTY 2

BALTIC BIRCH 1/2"

SLOTS ⌀0.190 x 3.000 TRAVEL

VESA 100 x 100 (3.937 SQUARE). TWO RAILS AT

X = 5.716 AND 9.654 FROM THE LEFT EDGE OF P1.

THE SLOTS GIVE 3.000 OF VERTICAL TRAVEL. THE MONITOR IS

ALIGNED TO THE P1 WINDOW, NOT TO THE BOX — SET IT BY EYE

THROUGH THE WINDOW WITH THE FACE PLATE TEMPORARILY FITTED,

DEPTH IS SET BY THE MONITOR, NOT BY THIS DRAWING. THE VESA

BOSS SITS AT A DIFFERENT DEPTH ON EVERY MODEL. SHIM BEHIND

P9 AT ASSEMBLY SO THE PANEL FACE LANDS 0.100 BEHIND P1.

CHECK BEFORE ORDERING THE MONITOR: MATTE, IPS, VESA 100,

AND IT MUST POWER ITSELF ON AFTER A MAINS CUT.

SITS IN THE BAY BELOW THE MONITOR ON TWO 0.500 SQ CLEATS.

SLIDES OUT FORWARD ONCE P4 IS OFF. RASPBERRY PI 4B MOUNTS

ON M2.5 STANDOFFS, 58.0 x 49.0 HOLE PATTERN.

U N L E S S O T H E R W I S E S P E C I F I E D DECIMAL .XX ± .03 .XXX ± .010
CUT PARTS PER SUPPLIER TOLERANCE BREAK SHARP EDGES · DEBURR ALL HOLES

E | E
D | D
C | C
B | B
A | A
3 2 8 0 K I O S K · R E V 1 S T A N D A L O N E | VINTAGE COMPUTER FEDERATION · INFOAGE

# P5-P8 CLEATS

CONCEPT — NOT RELEASED FOR PRODUCTION

D W G N O
302

R E V
A

S C A L E
1:4

S H E E T

### 8 OF 12

HARDWOOD, CLEAR

SEALED, SATIN BLACK

27.690

1.00 SQ

### P5 QTY 2

FRONT CLEAT, VERTICAL

ITEM 11 INSERTS ON P1 HOLE CENTRES

12.370

1.00 SQ

### P6 QTY 2

FRONT CLEAT, HORIZONTAL

ITEM 11 INSERTS ON P1 HOLE CENTRES

12.370

1.00 SQ

### P7 QTY 1

BUTTON RAIL

ITEM 11 INSERTS ON P1 HOLE CENTRES

27.690

0.75 SQ

### P8 QTY 2

REAR CLEAT, VERTICAL

### CLEAT NOTES

1. P5 AND P6 GLUE INSIDE THE BOX FLUSH WITH THE FRONT EDGE. P5 RUNS THE FULL

CAVITY HEIGHT; P6 FITS BETWEEN THEM.

2. P7 IS THE BUTTON RAIL. ITS CENTRELINE SITS 23.715 BELOW THE TOP OF P1, WHICH

IS 1.725 ABOVE THE BUTTON CENTRELINE — CLEAR OF THE SWITCH BODIES, WHICH

STAND ABOUT 1.000 PROUD BEHIND THE PLATE.

3. DRILL ITEM 11 THREADED INSERTS USING P1 AS THE TEMPLATE. CLAMP P1 IN PLACE,

SPOT THROUGH ALL 15 HOLES, REMOVE, THEN DRILL AND SET THE INSERTS.

4. NEVER DRIVE A FASTENER INTO A PLYWOOD EDGE. THAT IS WHAT THESE CLEATS ARE FOR.
5. P8 SETS BACK 0.750 FROM THE REAR EDGE SO P4 FINISHES FLUSH.
6. HARDWOOD PREFERRED FOR INSERT PULL-OUT STRENGTH. POPLAR OR MAPLE IS FINE.

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

## H O L E S C H E D U L E

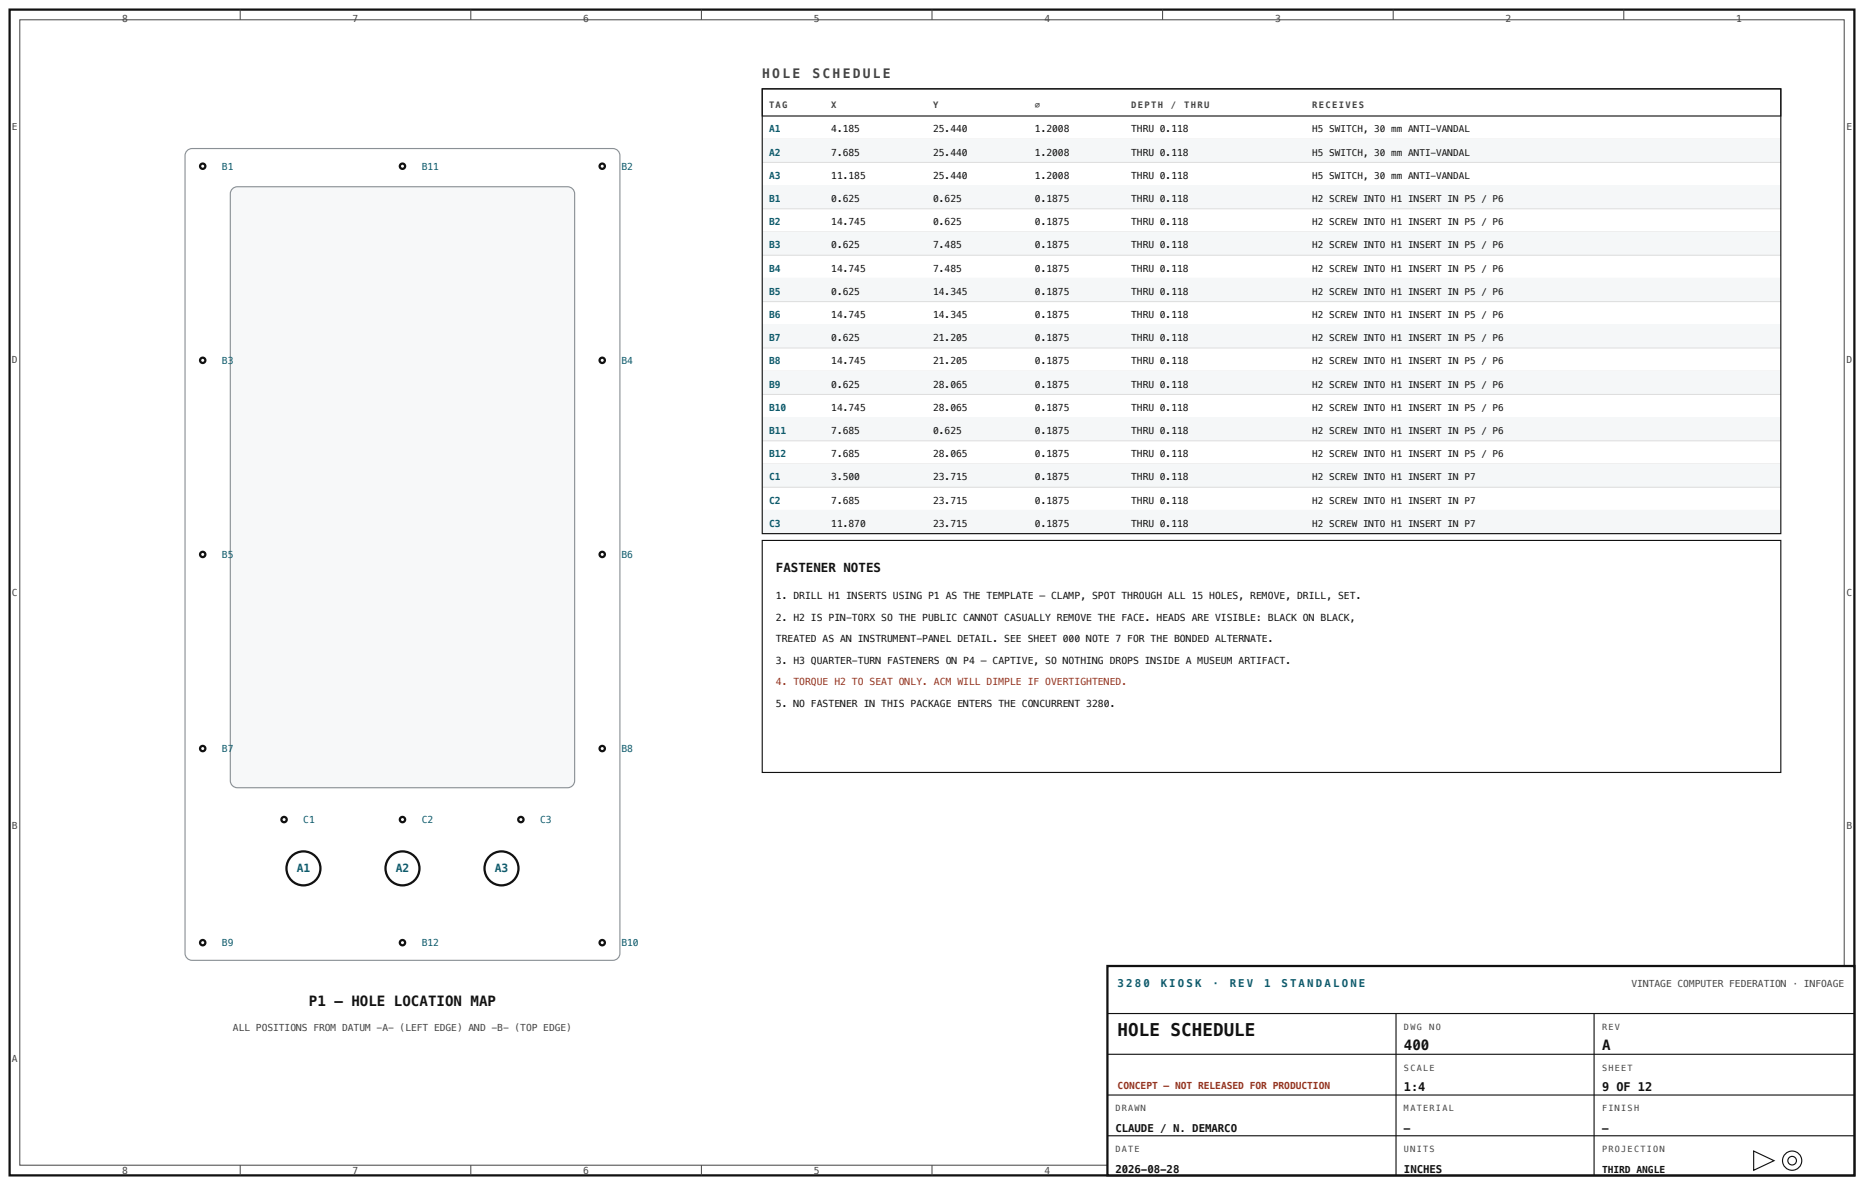
[picture p9: page 9]

1. DRILL H1 INSERTS USING P1 AS THE TEMPLATE — CLAMP, SPOT THROUGH ALL 15 HOLES, REMOVE, DRILL, SET.

2. H2 IS PIN-TORX SO THE PUBLIC CANNOT CASUALLY REMOVE THE FACE. HEADS ARE VISIBLE: BLACK ON BLACK,

TREATED AS AN INSTRUMENT-PANEL DETAIL. SEE SHEET 000 NOTE 7 FOR THE BONDED ALTERNATE.

3. H3 QUARTER-TURN FASTENERS ON P4 — CAPTIVE, SO NOTHING DROPS INSIDE A MUSEUM ARTIFACT.

4. TORQUE H2 TO SEAT ONLY. ACM WILL DIMPLE IF OVERTIGHTENED.

5. NO FASTENER IN THIS PACKAGE ENTERS THE CONCURRENT 3280.

ALL POSITIONS FROM DATUM -A- (LEFT EDGE) AND -B- (TOP EDGE)

CONCEPT — NOT RELEASED FOR PRODUCTION

E | E
D | D
C | C
B | B
A | A
3 2 8 0 K I O S K · R E V 1 S T A N D A L O N E | VINTAGE COMPUTER FEDERATION · INFOAGE

# ELECTRICAL

CONCEPT — NOT RELEASED FOR PRODUCTION

D W G N O
500

R E V
A

S C A L E

### NTS

S H E E T

### 10 OF 12

## P O W E R D I S T R I B U T I O N

### H6 IEC C14

FUSED INLET

### FUSED SPLIT

2 WAY, 120 VAC

### E3 MONITOR

24" IPS, INTERNAL PSU

### E2 PSU

5 V 3 A USB-C

### E1 PI 4B

4 GB

HDMI E4 RIGHT-ANGLE

MAINS IS CUT AT CLOSE BY AN AC TIMER. THE MONITOR MUST POWER ITSELF BACK ON.

TEST BEFORE PURCHASE: SWITCHED STRIP, KILL POWER, RESTORE, CONFIRM IT COMES BACK WITH NO INPUT.

## C O N T R O L W I R I N G

E1 RASPBERRY PI 4B

40-PIN HEADER

H5-1 BACK | 1 | GPIO5 | PIN 29
H5-2 HOME | 2 | GPIO6 | PIN 31
H5-3 NEXT | 3 | GPIO13 | PIN 33
GND | PIN 39

COMMON RETURN

### BUTTON CIRCUIT

THREE SPST-NO MOMENTARY SWITCHES, EACH ONE LEG TO A GPIO

AND ONE LEG TO A COMMON GROUND RETURN. NO EXTERNAL

PULL-UPS — ENABLE THE PI INTERNAL PULL-UPS IN SOFTWARE.

WIRE 22 AWG STRANDED. LEAVE 6 INCHES OF SLACK AT EACH

SWITCH SO THE PI TRAY CAN SLIDE OUT WITHOUT UNPLUGGING.

STRAIN-RELIEVE THE LOOM TO P7 BUTTON RAIL.

IF THE SWITCHES ARE ILLUMINATED, THE LED LEG IS SEPARATE —

FEED IT FROM 3V3 THROUGH A RESISTOR, NOT FROM THE GPIO.

GPIO ASSIGNMENT MUST MATCH src/controller/. CHANGE ONE,

CHANGE BOTH.

E | E
D | D
C | C
B | B

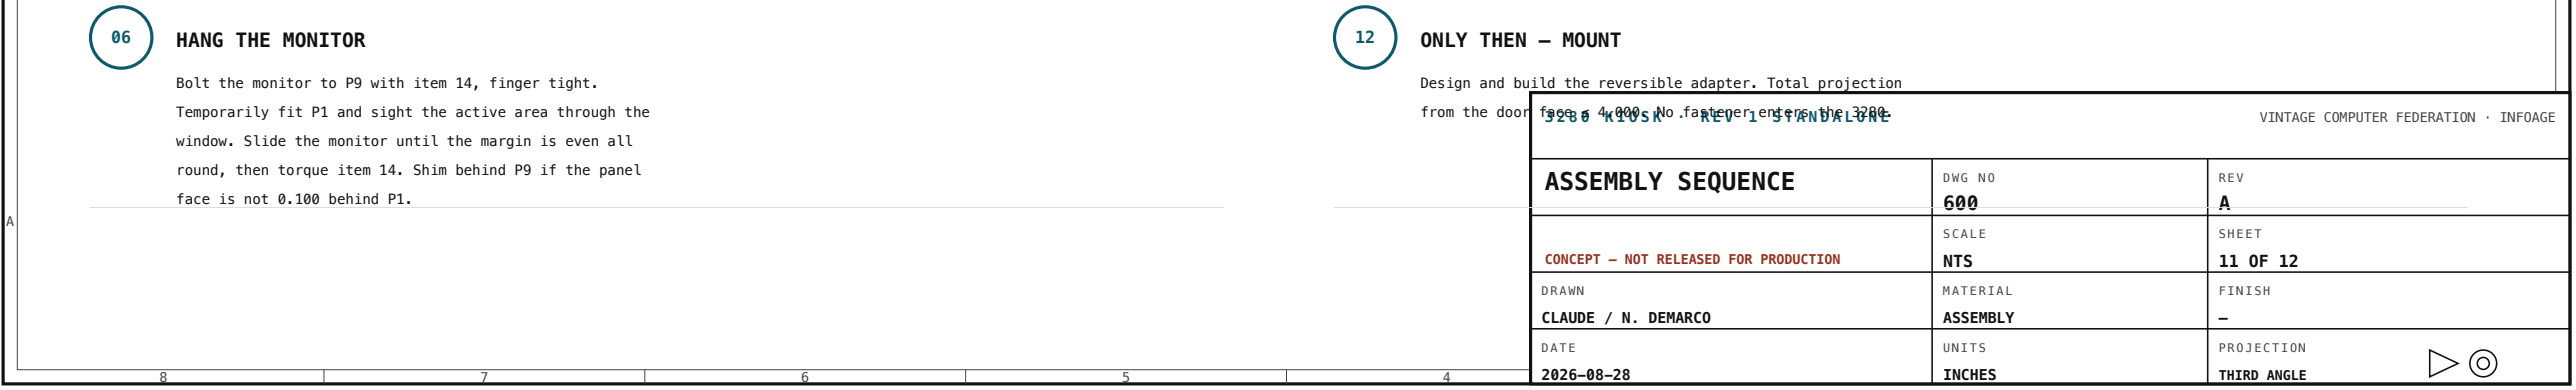
[picture p10: figure]
ASSEMBLY SEQUENCE; CONCEPT — NOT RELEASED FOR PRODUCTION; S C A L E NTS; ASSEMBLY; 06 HANG THE MONITOR; face is not 0.100 behind P1.; 12 ONLY THEN — MOUNT

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

## 01 PREPARE THE PANELS

Cut P2, P3, P4, P9, P10 to size. Sand to 180.

Seal and paint every internal surface satin black before

assembly — bare ply reflects through the window.

## 02 BUILD THE BOX

Glue and screw P2 sides to P3 top and bottom, item 17,

4 per joint, pilot drilled. Clamp square: measure both

diagonals, within 0.06 of each other.

## 03 FIT THE CLEATS

Glue P5 vertical cleats flush with the front edge, then P6

between them. Glue P7 button rail with its centreline

23.715 below the top of the box. Glue P8 rear cleats set

back 0.750 from the rear edge.

## 04 SET THE THREADED INSERTS

Clamp P1 to the front. Spot through all 15 holes. Remove

P1, drill for item 11 and set the inserts. Do not skip the

clamp-and-spot — the holes must match, not merely measure.

## 05 MOUNT THE VESA RAILS

Fit P9 rails at X = 5.716 and 9.654 from the left edge.

Glue and screw to P3 top and bottom. Leave the monitor

bolts loose for now.

Bolt the monitor to P9 with item 14, finger tight.

Temporarily fit P1 and sight the active area through the

window. Slide the monitor until the margin is even all

round, then torque item 14. Shim behind P9 if the panel

## 07 FIT THE SWITCHES

Item 15 into the three ⌀1.2008 holes in P1 from the front.

Nut from behind. Do not overtighten — ACM will dimple.

## 08 WIRE

Per sheet 500. Common return to one GND pin. Leave 6 in of

slack at each switch. Strain-relieve the loom to P7.

## 09 FIT THE PI AND POWER

P10 tray into the bay on its cleats. Pi on M2.5 standoffs.

H6 inlet in the lower rear. Route HDMI and DC downward with

right-angle plugs — straight plugs will not fit.

## 10 CLOSE UP

Fit P1 with item 12. Torque to seat only. Fit P4 with item

13. Apply the BACK / HOME / NEXT vinyl legends, centred

under each button.

## 11 BENCH TEST — ONE WEEK

Run the complete kiosk on a table. Confirm: all three

buttons, boot to the app unattended, and recovery from a

mains cut with no human input. Do not skip the week.

Design and build the reversible adapter. Total projection

from the door face ≤ 4.000. No fastener enters the 3280.

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

# INSPECTION

CONCEPT — NOT RELEASED FOR PRODUCTION

D W G N O
700

R E V
A

S C A L E

### NTS

S H E E T

### 12 OF 12

## I N S P E C T I O N D I M E N S I O N S

Check these before the kiosk leaves the bench. Anything out of tolerance here shows up on the machine.

# | F E A T U R E | N O M I N A L | T O L E R A N C E | M E T H O D | W H Y I T M A T T E R S

1 | P1 OVERALL | 15.370 x 28.690 | ± 0.030 | TAPE / CALIPER | SUPPLIER CUT — SPOT CHECK ONLY
2 | P1 WINDOW | 12.170 x 21.240 | ± 0.030 | CALIPER | MUST NOT CROP THE ACTIVE AREA
3 | BUTTON CENTRELINE BELOW TOP EDGE | 25.440 | ± 0.030 | TAPE FROM DATUM -B- | SETS ADA HEIGHT — CRITICAL
4 | BUTTON PITCH | 3.500 | ± 0.020 | CALIPER | —
5 | BUTTON CUTOUT | ⌀1.2008 | +0.010 / -0.000 | PIN / CALIPER | VERIFY AGAINST SWITCH DATASHEET
6 | BOX DIAGONALS, FRONT OPENING | EQUAL | WITHIN 0.060 | TAPE, CORNER TO CORNER | SQUARENESS
7 | OVERALL DEPTH, ASSEMBLED | 3.250 | ± 0.040 | CALIPER AT 4 CORNERS | FEEDS THE 4.000 §307.2 BUDGET
8 | P1 FLUSH TO BOX EDGE | 0.000 | ± 0.020 | STRAIGHTEDGE | NO PROUD EDGE TO CATCH
9 | MONITOR MARGIN IN WINDOW | EVEN ALL ROUND | ± 0.060 | EYE + RULE | ADJUST AT P9 SLOTS
10 | SERVICE AIR, MONITOR TO P4 | 0.732 MIN | MIN | DEPTH GAUGE | CABLE BEND CLEARANCE
11 | ALL 15 FIXINGS ENGAGE | 15 OF 15 | — | BY HAND | NO STRIPPED INSERT
12 | P4 REMOVES AND REFITS | — | — | BY HAND | WITHOUT TOOLS OR LOOSE PARTS

## GO / NO-GO ON THE MONITOR

1. IT MUST POWER ITSELF BACK ON AFTER A MAINS CUT.

The exhibit is on an AC timer. Many monitors return to standby

and need a button press — that is a black screen every morning.

Test: switched strip, kill power, restore, confirm it comes back

with no input. This is go / no-go, not a preference.

2. MATTE ONLY. Overhead lights and daylight; glossy panels mirror them.

## SIGN-OFF

INSPECTED BY

DATE

BENCH TEST START

BENCH TEST END

RELEASED TO INSTALL
