nickdnj/3280-kiosk/mechanical/photos/me1-door-width-tape.jpg

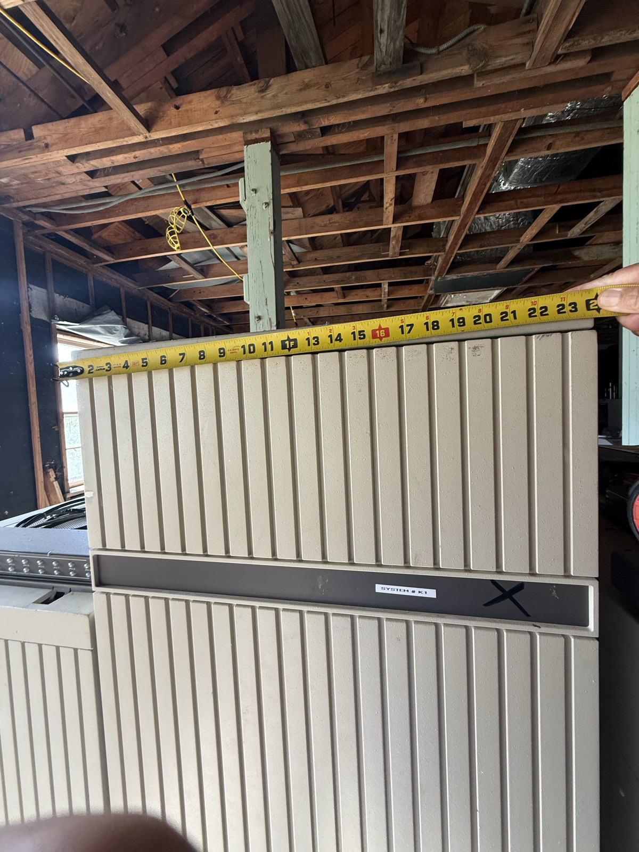
mechanical/photos/me1-door-width-tape.jpg
