nickdnj/3280-kiosk/mechanical/photos/me1-height-tape.jpg

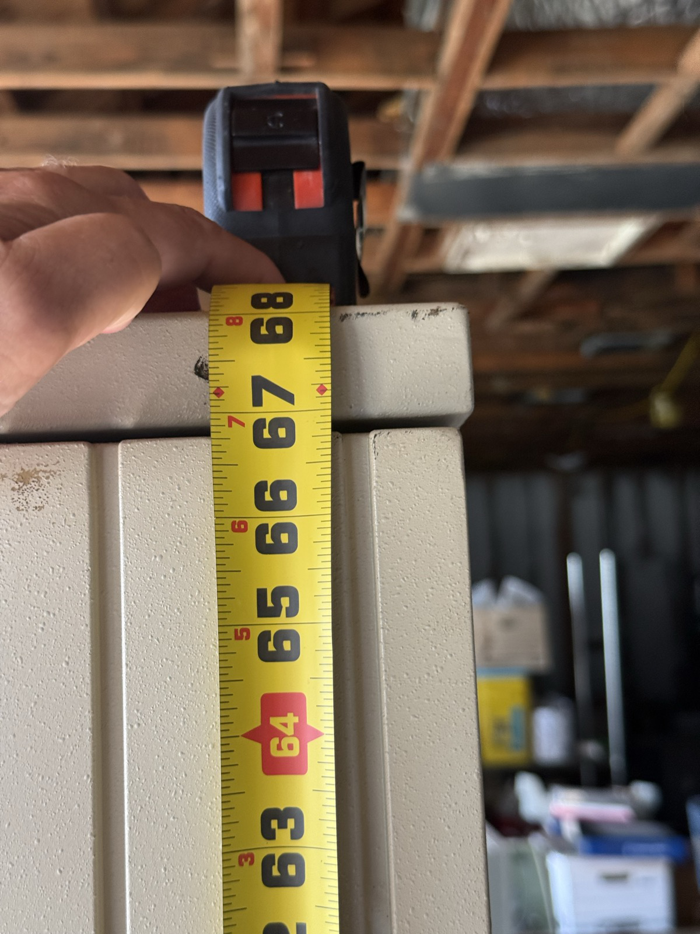
mechanical/photos/me1-height-tape.jpg
