nickdnj/3280-kiosk/mechanical/photos/me1-opening-width-tape.jpg

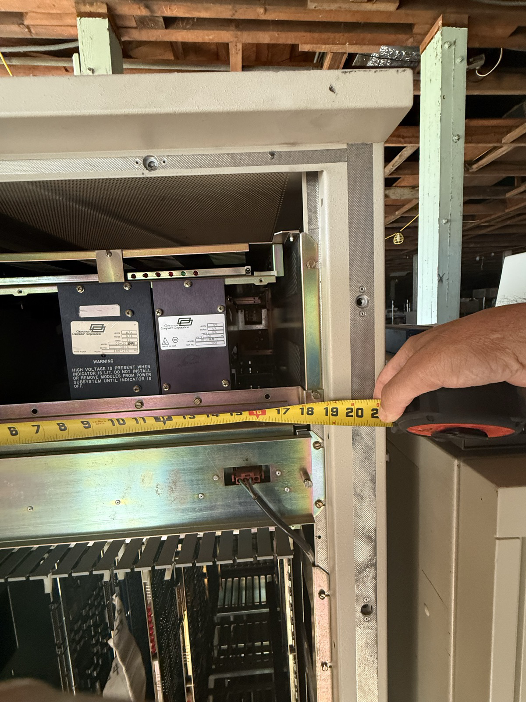
mechanical/photos/me1-opening-width-tape.jpg
