nickdnj/3280-kiosk/mechanical/photos/me1-vertical-32.jpg

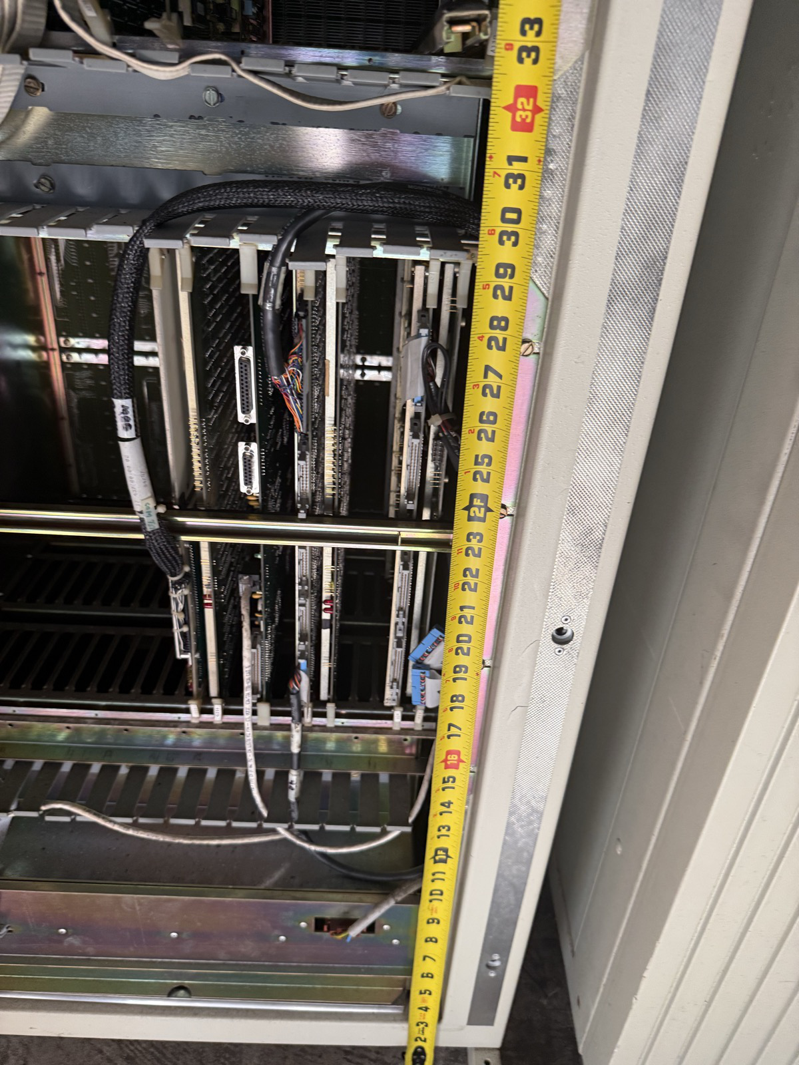
mechanical/photos/me1-vertical-32.jpg
