nickdnj/3280-kiosk/mechanical/photos/me1-vertical-48.jpg

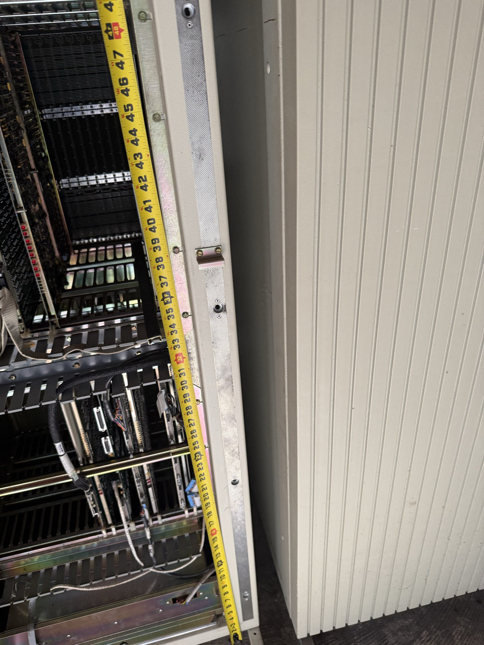
mechanical/photos/me1-vertical-48.jpg
