nickdnj/3280-kiosk/src/kiosk-app/assets/mont/defense.jpg

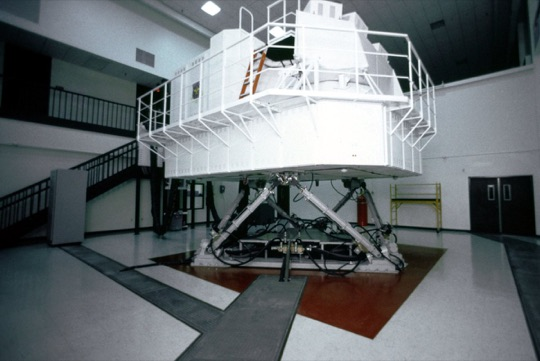
src/kiosk-app/assets/mont/defense.jpg
