nickdnj/3280-kiosk/src/kiosk-app/assets/mont/finance.jpg

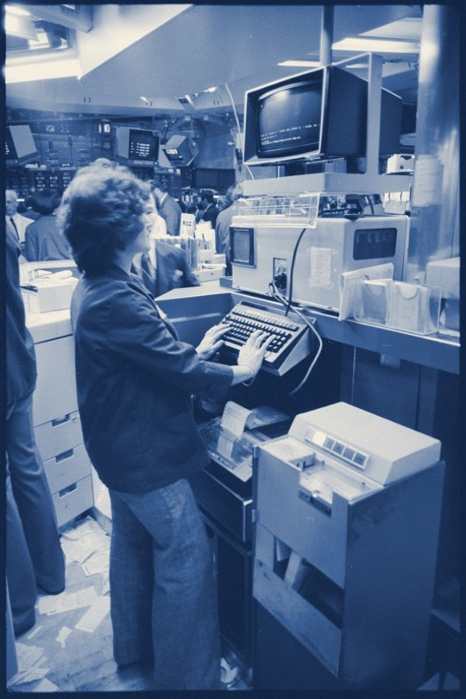
src/kiosk-app/assets/mont/finance.jpg
