nickdnj/3280-kiosk/src/kiosk-app/assets/mont/space.jpg

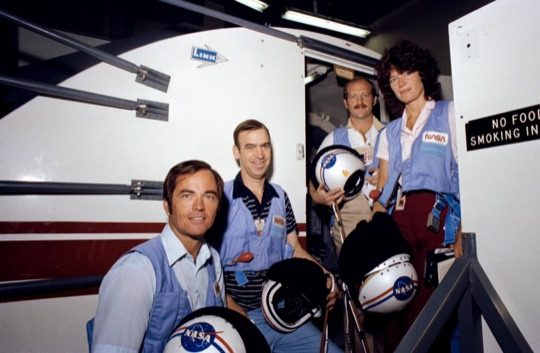
src/kiosk-app/assets/mont/space.jpg
