nickdnj/3280-kiosk/src/kiosk-app/assets/mont/weather.jpg

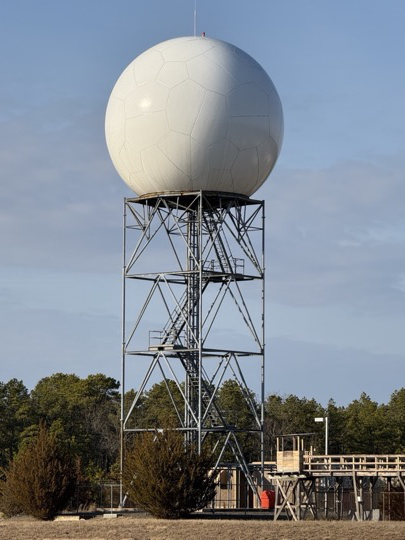
src/kiosk-app/assets/mont/weather.jpg
