nickdnj/3280-kiosk/src/kiosk-app/assets/posters/poster-B.jpg

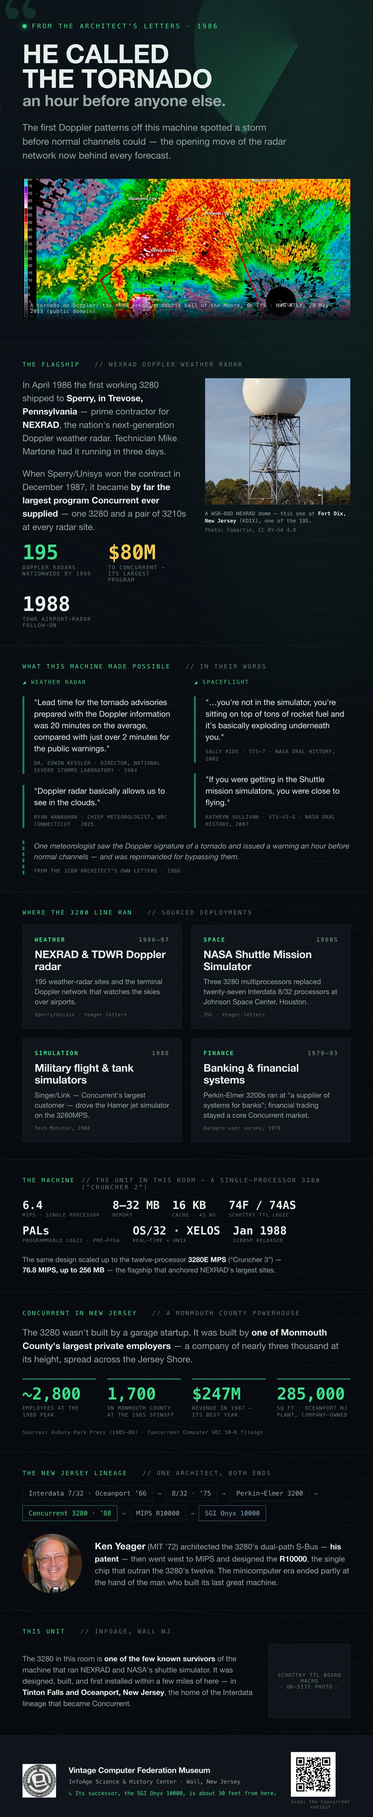
src/kiosk-app/assets/posters/poster-B.jpg
