nickdnj/3280-kiosk/src/kiosk-app/assets/renders/interior-open.jpg

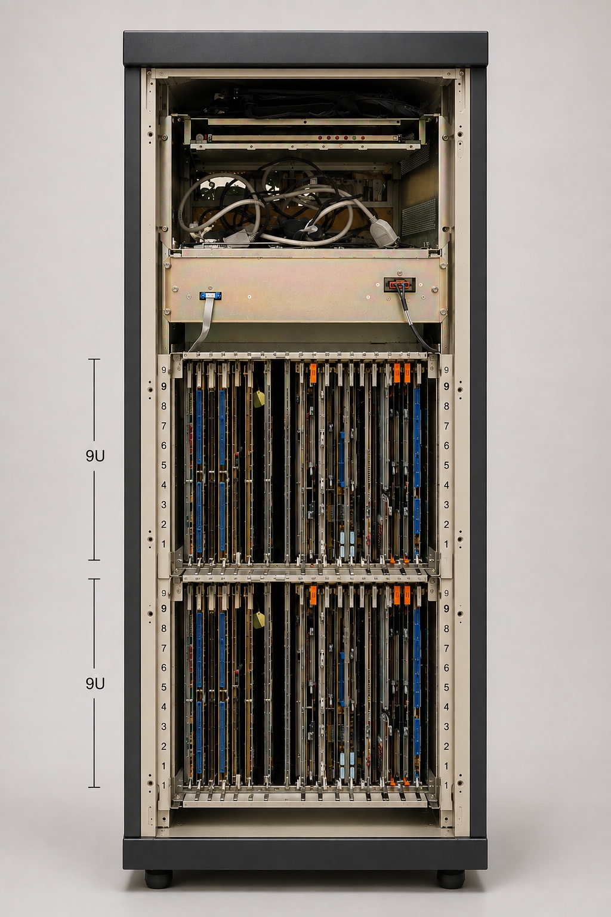
src/kiosk-app/assets/renders/interior-open.jpg
