nickdnj/3280-kiosk/src/kiosk-app/assets/renders/machine.jpg

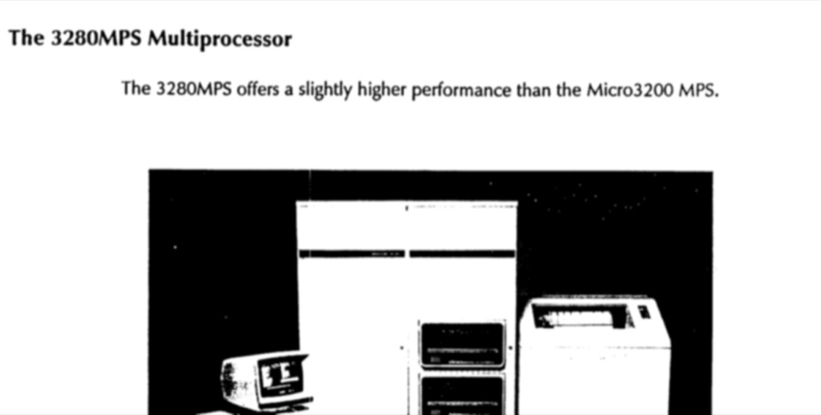
src/kiosk-app/assets/renders/machine.jpg
