nickdnj/3280-kiosk/src/kiosk-app/assets/renders/njplant.jpg

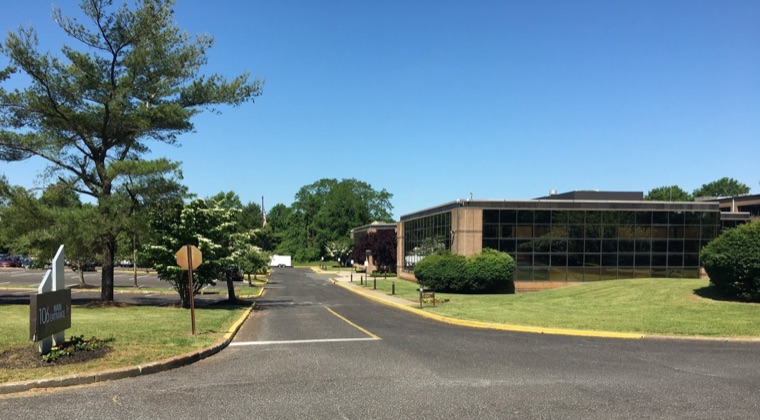
src/kiosk-app/assets/renders/njplant.jpg
