nickdnj/3280-kiosk/src/kiosk-app/assets/renders/onyx.jpg

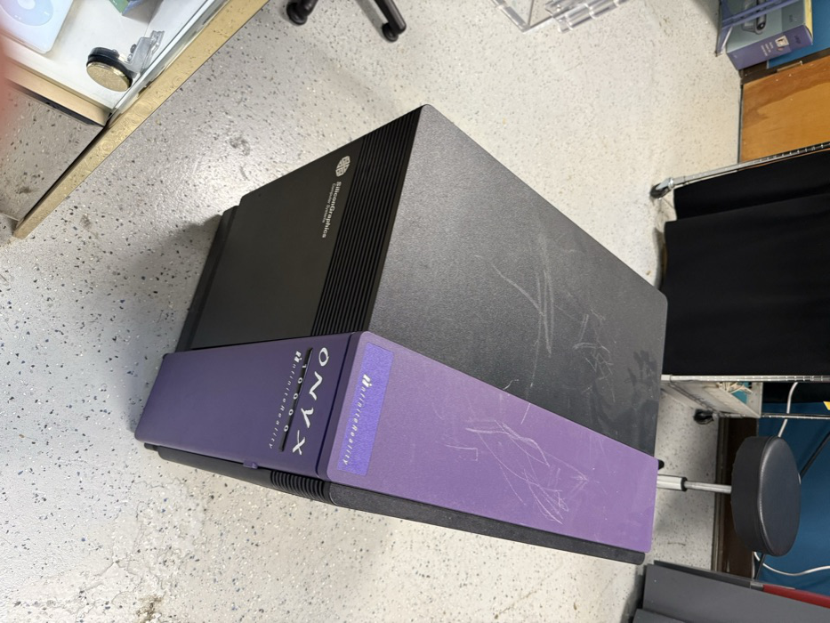
src/kiosk-app/assets/renders/onyx.jpg
