nickdnj/3280-kiosk/src/kiosk-app/assets/renders/r10000.jpg

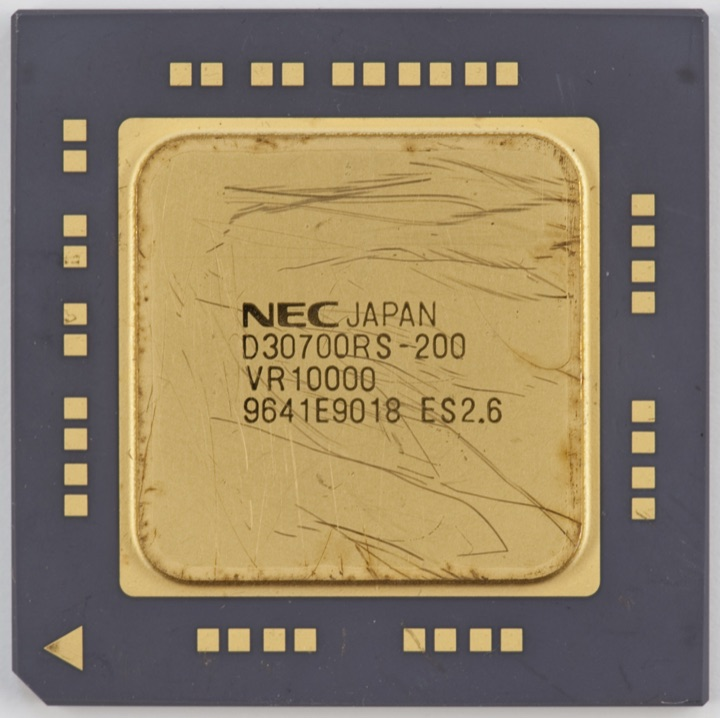
src/kiosk-app/assets/renders/r10000.jpg
