nickdnj/3280-kiosk/src/kiosk-app/assets/renders/radar.jpg

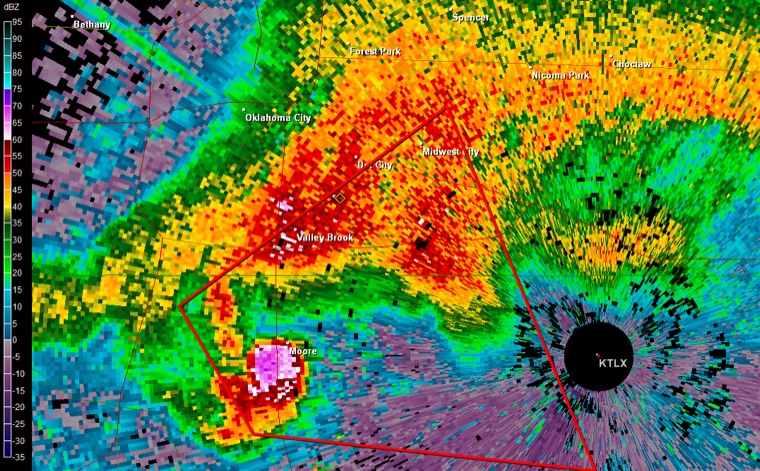
src/kiosk-app/assets/renders/radar.jpg
