nickdnj/3280-kiosk/src/kiosk-app/assets/renders/shell.jpg

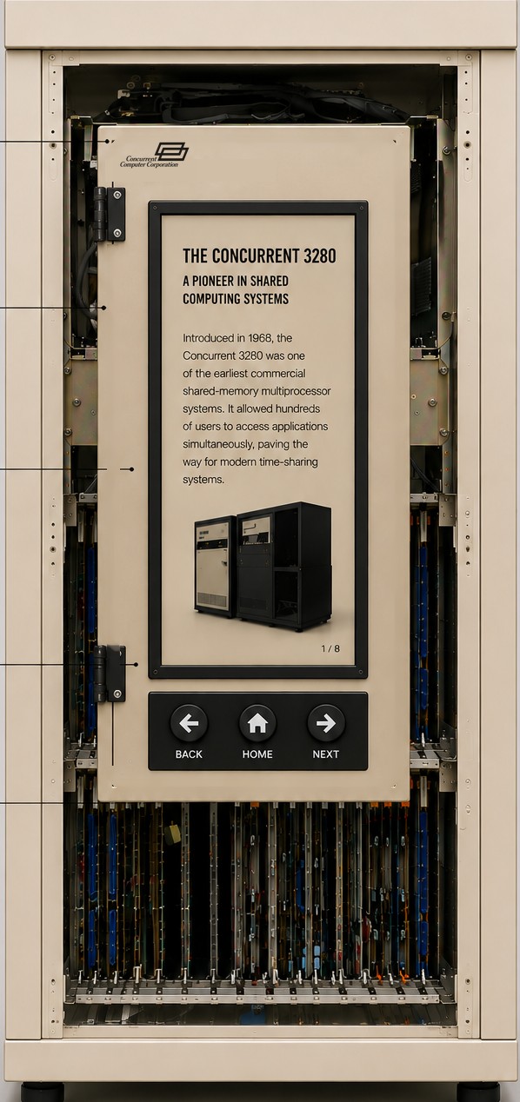
src/kiosk-app/assets/renders/shell.jpg
