nickdnj/3280-kiosk/src/kiosk-app/assets/renders/yeager.jpg

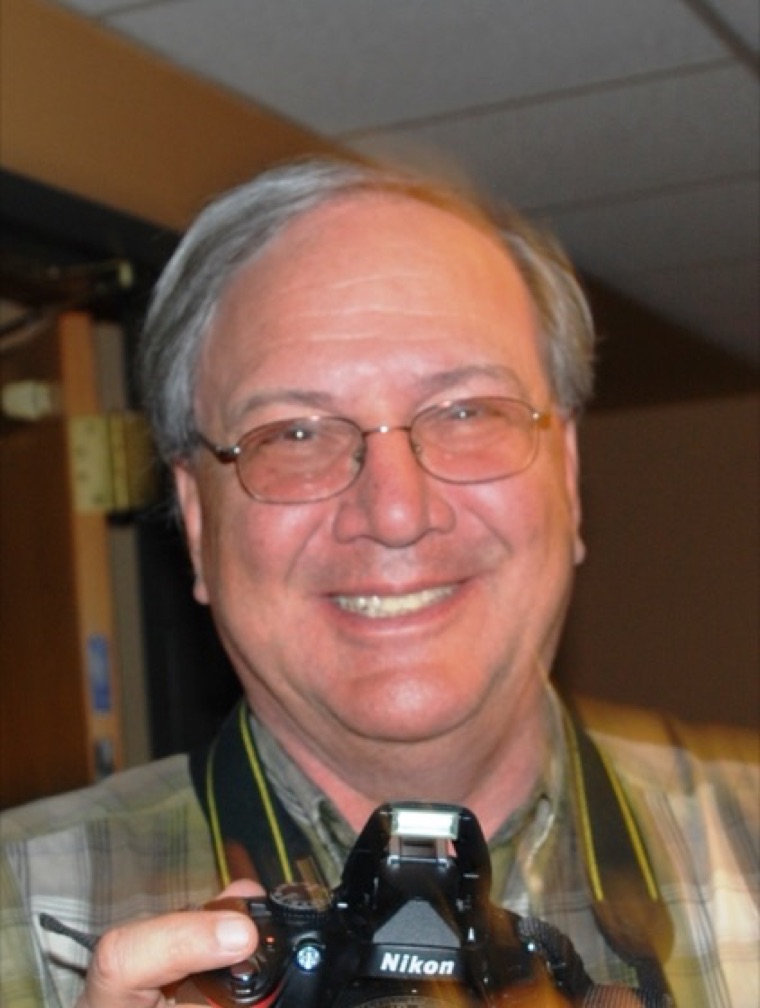
src/kiosk-app/assets/renders/yeager.jpg
